CatKoishi/SAF775X-Radio/Hardware/GD32F303RC/GD32使用FPU以及DSP库的操作方法.pdf

# GD32 使用 FPU 以及 DSP 库的操作方法

在 GD32 中的 F3 系列插件有两个版本，V1.0.1 的插件是不支持 FPU 的，V2.0.0 的版本 才支持，如果安装的版本在 Target 中找不到下列的选项，请先安装新版本的插件。
在 F4 系列和 E103 系列插件都是支持 FPU 的。

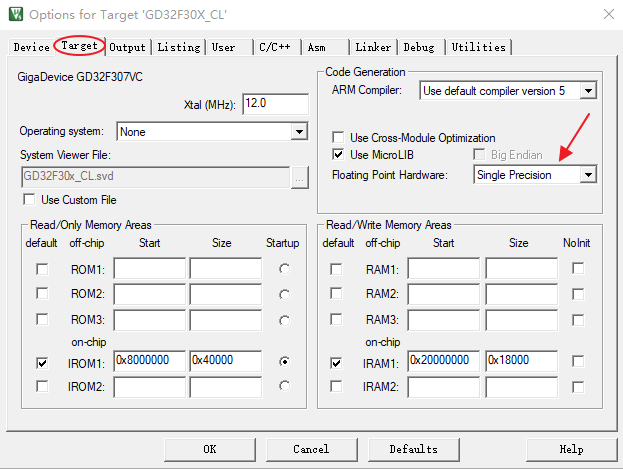
[picture p2: figure]

## 打开 FPU 的步骤

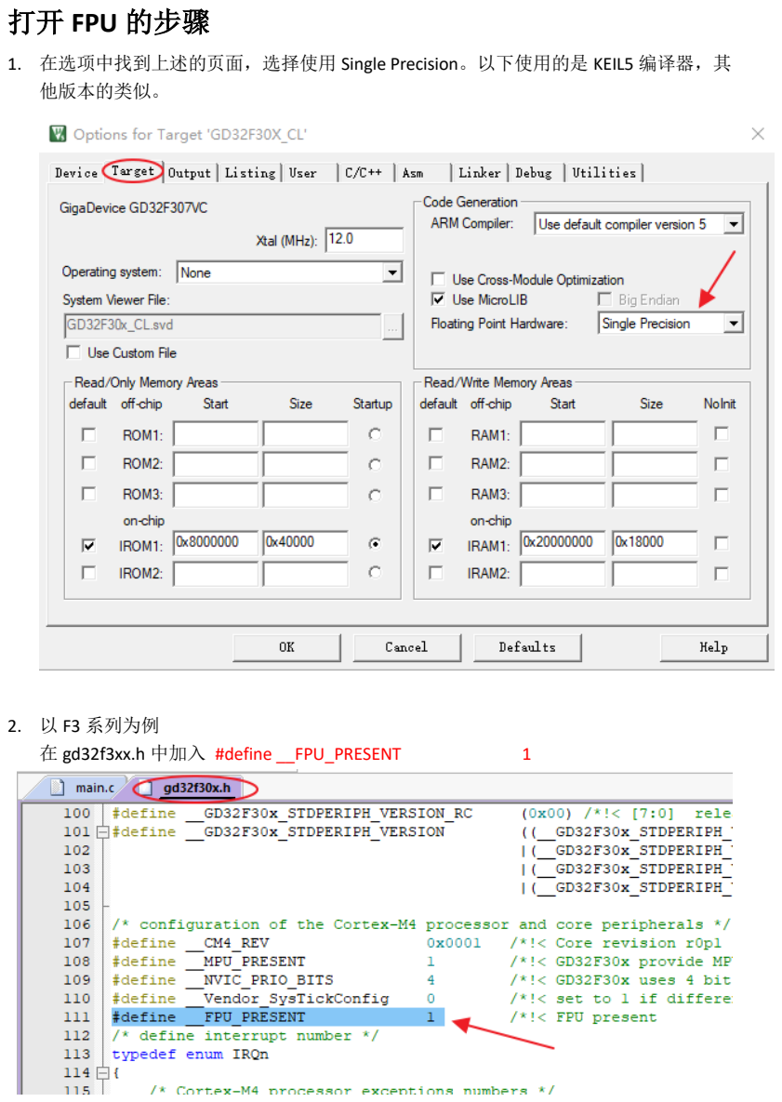
[picture p3: page 2]

1. 在选项中找到上述的页面，选择使用 Single Precision。以下使用的是 KEIL5 编译器，其 他版本的类似。
2. 以 F3 系列为例
在 gd32f3xx.h 中加入 #define __FPU_PRESENT | 1

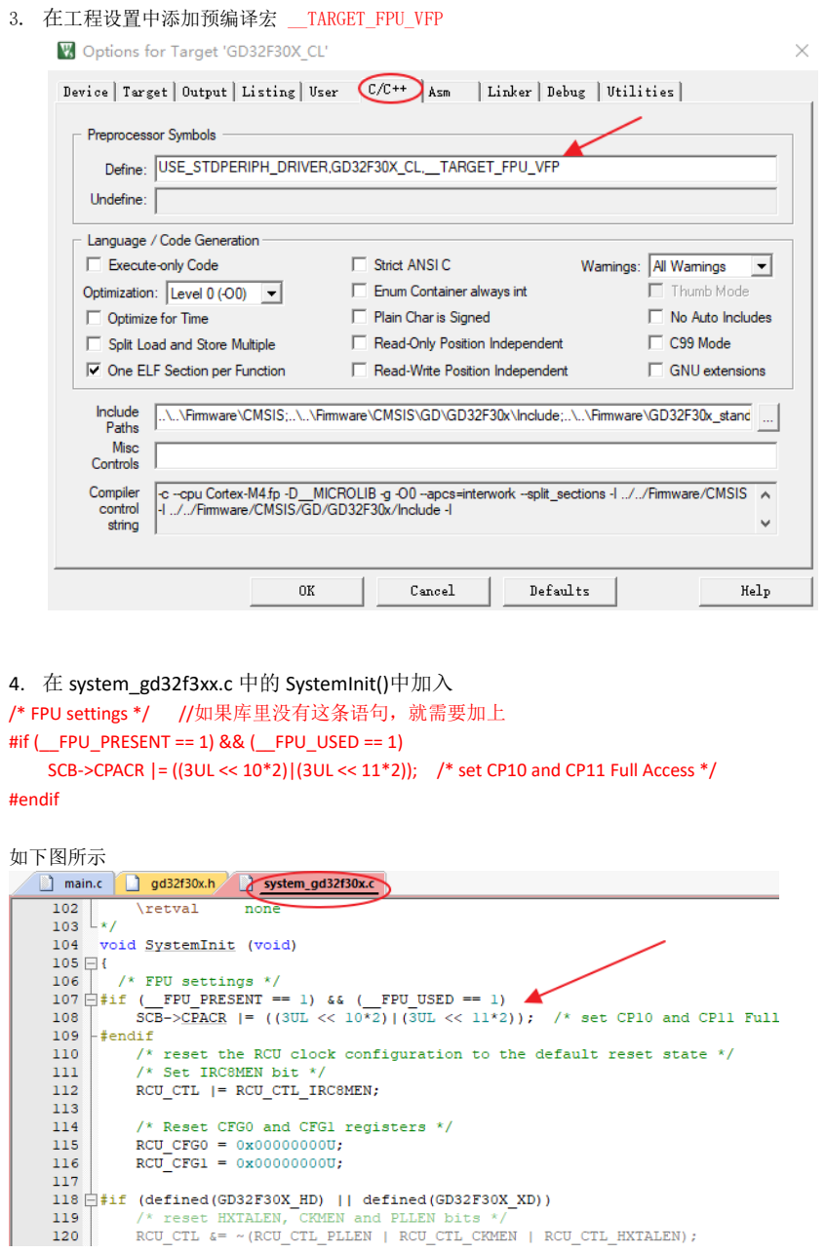
[picture p4: page 3]

3. 在工程设置中添加预编译宏 __TARGET_FPU_VFP
4. 在 system_gd32f3xx.c 中的 SystemInit()中加入
/* FPU settings */ //如果库里没有这条语句，就需要加上
#if (__FPU_PRESENT == 1) && (__FPU_USED == 1)

SCB->CPACR |= ((3UL << 10*2)|(3UL << 11*2)); /* set CP10 and CP11 Full Access */ #endif

如下图所示

使用 F4 系列和 E103 系列
1.同样在 gd32f4xx.h 中加入 #define __FPU_PRESENT | 1
2. 在工程设置中添加预编译宏 __TARGET_FPU_VFP
3.在 system_gd32f4xx.c 中的 SystemInit()中加入
/* FPU settings */ //如果库里没有这条语句，就需要加上
#if (__FPU_PRESENT == 1) && (__FPU_USED == 1)

SCB->CPACR |= ((3UL << 10*2)|(3UL << 11*2)); /* set CP10 and CP11 Full Access */ #endif
5. 重新编译下载烧录即可

## 检查 FPU 是否打开

1. 在 jlink 调试控制界面下，输入语句
mem32 0XE000ED88 1
具体看下图，得到的值为 00F0 0000，证明 FPU 已经开启

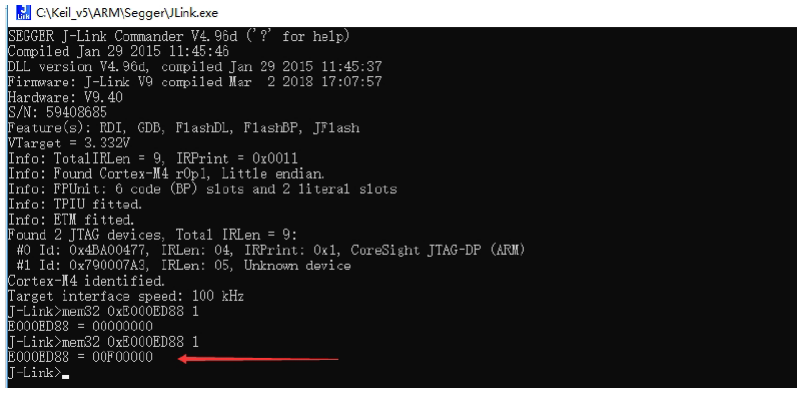
[picture p5: figure]

2. KEIL 调试浮点运算反汇编界面中会有 VLDR VADD 等浮点运算寄存器 如下图所示

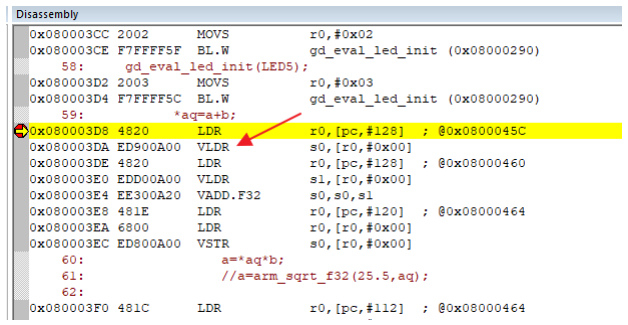
[picture p6: figure]

没开启的情况如下图

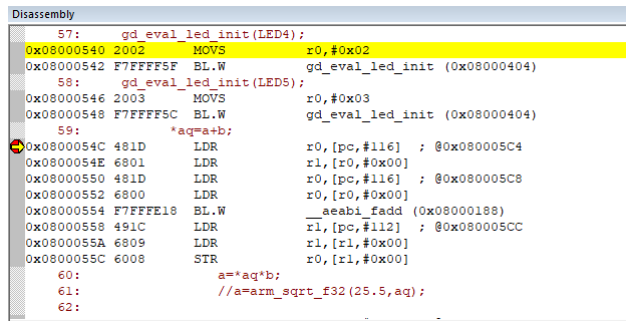
[picture p7: figure]

## 使用 DSP 的步骤

1. 打开 FPU 之后，在工程中添加 ARM 官方浮点库 ”arm_cortexM4lf_math.lib” "arm_math.h"

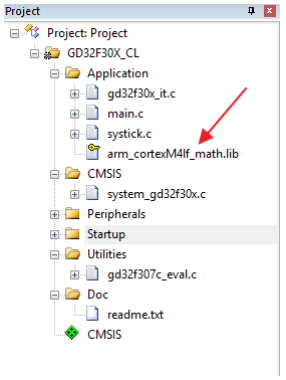
[picture p8: figure]

2. 在需要使用浮点库函数的.c 文件中添加 #include "arm_math.h" （这个头文件中包含所 有的函数接口）
3. 在工程设置中添加预编译宏 ARM_MATH_CM4

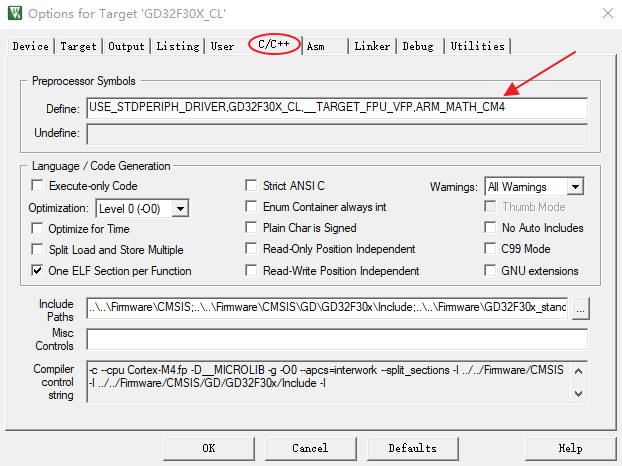
[picture p9: figure]
