CatKoishi/SAF775X-Radio/Hardware/IMG_20230905_173325.jpg

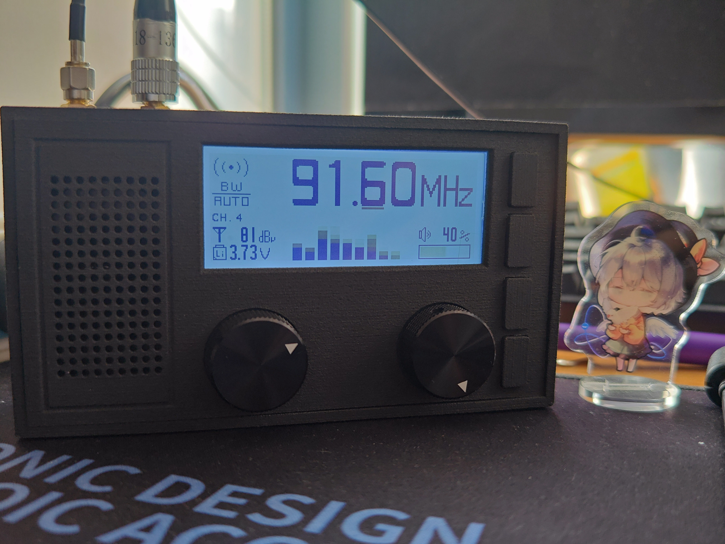
Hardware/IMG_20230905_173325.jpg
