CatKoishi/SAF775X-Radio/Hardware/GD32F303RC/MINI-GD32F303RCV4.0.pdf

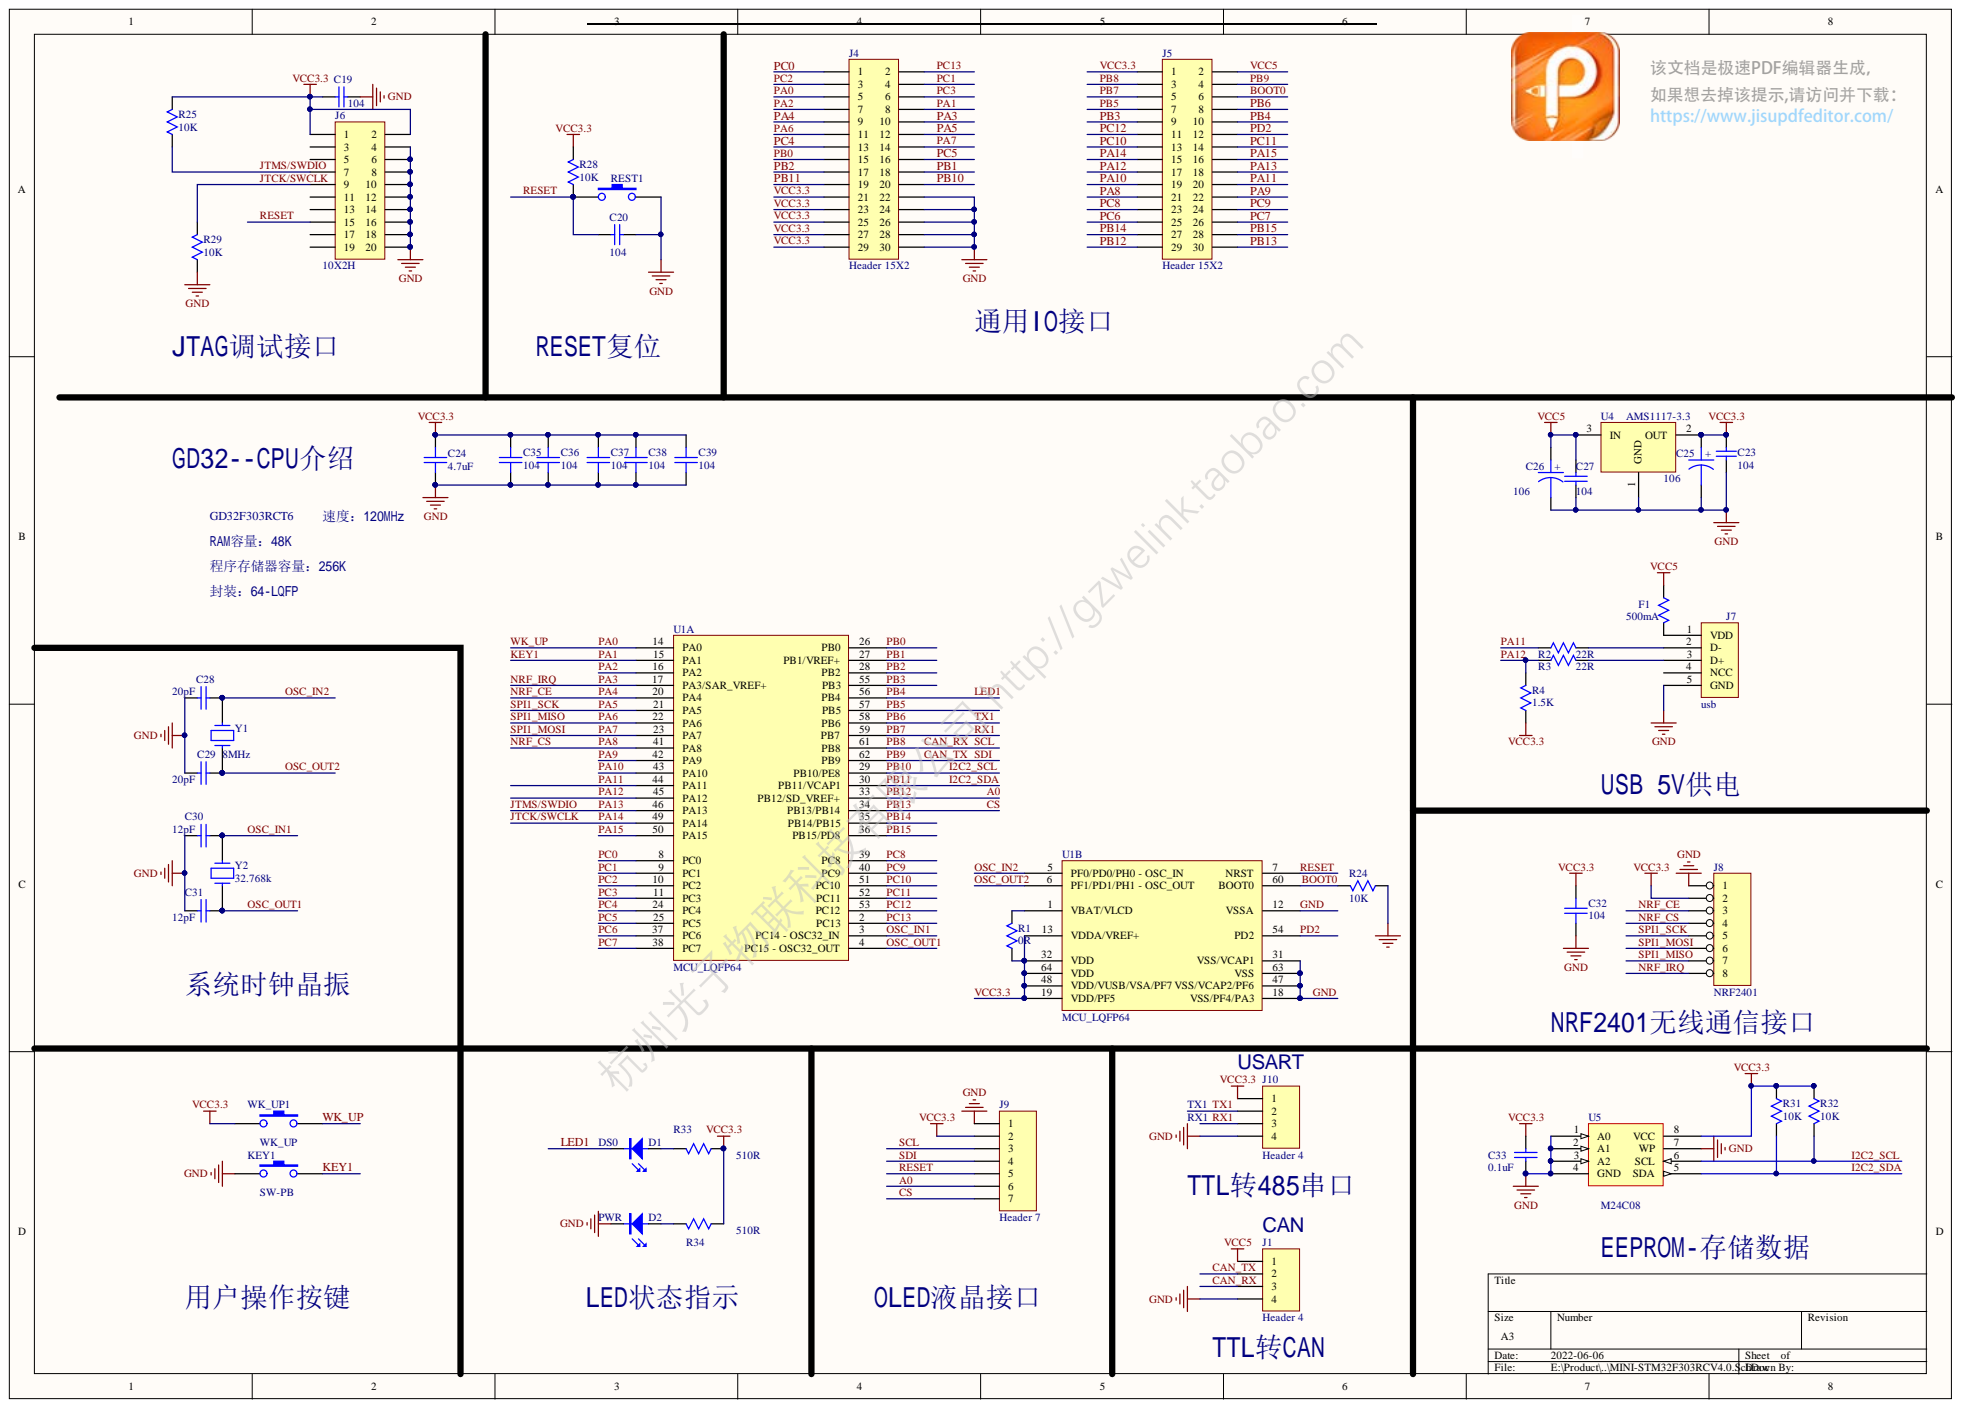
[picture p19: page 1]

该文档是极速PDF编辑器生成，
如果想去掉该提示,请访问并下载：
https://www.jisupdfeditor.com/ (https://www.jisupdfeditor.com?watermark)
