CatKoishi/SAF775X-Radio/User/hardware/SAF775X.c

#include "SAF775X.h"
#include "gd32f30x.h"
#include "stdarg.h"
#include "systick.h"
#include "iic_sw.h"
#include "Dirana3_ABB_E7A0.h"
#include "Dirana3_ABB_E7A1.h"
#include "Dirana3BasicDSP.h"

#define WORD_LOW_BYTE(a)     ((unsigned char)(a & 0x00FF))
#define WORD_HIGH_BYTE(a)    ((unsigned char)(a >> 8))
/************************************************************************************************************************************/

struct Dirana3Radio *sys;

static void SetAudioSampleRate(uint8_t sampleRate);

extern struct RDSData sRDSData;

/************************************************************************************************************************************/

const uint8_t nBandRFMode[NUM_BANDS] = 
{ RFMODE_FM, RFMODE_AM, RFMODE_AM, RFMODE_AM };

//不同波段的步进值
uint16_t nBandStep[NUM_BANDS][NUM_STEPS] = 
{
	{ 1, 10 , 0  , 0    },	//x10 KHz  FM
	{ 1,  9 , 0  , 0    },  //x1  KHz  LW
	{ 1,  9 , 100, 0    },  //x1  KHz  MW
	{ 1,  5 , 100, 1000 }   //x1  KHz  SW
};

//不同波段的步进值的数量
const uint8_t nBandStepNum[NUM_BANDS] = 
{ 2, 2, 3, 4 };

uint8_t nBandStepATS[NUM_BANDS] = 
{ 10, 1, 9, 5};

const uint16_t nFastATS[14][2] = 
{
	{2300, 2500},
	{3200, 3400},
	{3900, 4000},
	{4750, 5060},
	{5900, 6200},
	{7100, 7600},
	{9100, 10000},
	{11600, 12100},
	{13500, 13870},
	{15100, 15800},
	{17480, 17900},
	{18900, 19020},
	{21450, 21850},
	{25600, 26100}
};

const uint16_t nFMATSRegion[4][2] = {
	{8700,10800},
	{6500,7300},
	{7600,9000},
	{8750,10800},
};

const int16_t nBandFMin[NUM_BANDS] =
{ 6500, 144, 522, 2300 };

const int16_t nBandFMax[NUM_BANDS] =
{ 10800, 288, 1710, 27000 };

/************************************************************************************************************************************/

const uint8_t DSP_FIRM0_PRODUCTION[] =
{
	1,0xE8,
	0x81,0x2C,
	0
};

const uint8_t DSP_FIRM1_PRODUCTION[] =
{
	//Load Firmware Version 7.1
	25,0xE1,0x9C,0x40,0xCC,0x6B,0x8C,0x70,0xE4,0xD6,0x01,0xBB,0xDB,0x00,0x45,0x75,0x2C,0x68,0xA1,0x39,0x33,0x53,0xF5,0x4E,0x9D,0x8F,
	25,0xE1,0x2B,0xC3,0xA0,0x0D,0xC7,0x85,0xA4,0x9D,0x99,0x4D,0x5C,0x15,0x44,0x08,0x16,0x52,0x8E,0x6C,0xAA,0xF5,0xB5,0x09,0x08,0x25,
	25,0xE1,0x9A,0xBE,0xEB,0x91,0xCC,0x98,0xBC,0x4D,0x89,0x8E,0x0F,0x18,0x8C,0x3A,0xD3,0xD2,0x11,0xA7,0x49,0xE8,0x69,0x4A,0x3C,0x22,
	25,0xE1,0xA8,0x90,0xF1,0x8B,0x74,0xC3,0x97,0xA1,0xEB,0x25,0x4C,0x56,0xBC,0x29,0x46,0x85,0xA1,0x52,0x22,0x75,0x3E,0xBD,0xC6,0xFC,
	25,0xE1,0x4B,0x76,0xE7,0x85,0x74,0xBB,0x2E,0x3E,0x14,0xFE,0xAF,0xAC,0x37,0xF0,0x8A,0xA2,0x9D,0x90,0x9E,0xC3,0xC8,0xC9,0xEB,0x22,
	25,0xE1,0x6E,0x24,0x4B,0x07,0xDD,0xC5,0x43,0x36,0x0F,0x71,0x9D,0x06,0x64,0x69,0x77,0x91,0xD6,0x58,0x29,0xB4,0x41,0xFF,0xD6,0x65,
	25,0xE1,0x34,0x04,0x67,0xE1,0x77,0xC5,0x34,0xB7,0xCD,0x37,0x32,0x4E,0x56,0x9F,0x77,0xE8,0x5C,0x60,0x13,0x34,0x7E,0x44,0xD3,0xEE,
	25,0xE1,0x46,0x8F,0x9F,0x06,0xD3,0x9E,0x22,0x38,0xA0,0x62,0x28,0x45,0x26,0xC4,0x80,0x72,0xF4,0x22,0xF0,0x4B,0x45,0xD9,0xA1,0x7D,
	25,0xE1,0x54,0xD9,0x0D,0x88,0x02,0x9C,0x95,0x51,0xAE,0x97,0x91,0xA1,0xB8,0x66,0x33,0xE4,0x87,0x1D,0xC7,0xB8,0x00,0x1E,0x7B,0x30,
	25,0xE1,0x3C,0xE5,0x08,0x7F,0x39,0xC4,0x54,0x2C,0x3D,0xFF,0xAF,0xF8,0x1D,0xF5,0xDB,0x8F,0xE9,0xEE,0x9F,0x1B,0x38,0x42,0x96,0x48,
	25,0xE1,0xEB,0xFC,0x0A,0x05,0x68,0x9B,0x4E,0x9B,0xC7,0xDF,0x40,0x11,0x6E,0xFA,0x01,0x2F,0xD9,0x3E,0x60,0xEA,0xEB,0x13,0x3D,0x73,
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

void Set_REG(uint8_t addr, uint8_t* data, uint8_t size)
{
	I2C_Start(DSP_I2C_ADDR&0xFE);
	I2C_WriteByte(addr);
	
	for(uint16_t i = 0;i<size;i++)
	{
		I2C_WriteByte(data[i]);
	}
	
	I2C_Stop();
}

void Set_REGFree(int len, ...)
{
	uint8_t tmp;
	uint32_t i;
	va_list vArgs;
	va_start(vArgs, len);
	
	I2C_Start(DSP_I2C_ADDR&0xFE);
	for(i=0;i<len;i++)
	{
		tmp = va_arg(vArgs, uint32_t);
		I2C_WriteByte(tmp);
	}
	I2C_Stop();
	
	va_end(vArgs);
}


void Get_REG(uint8_t addr, uint8_t* data, uint8_t size)
{
	uint16_t i = 0;
	I2C_Start(DSP_I2C_ADDR&0xFE);
	I2C_WriteByte(addr);
	I2C_Restart(DSP_I2C_ADDR|0x01);
	
	for(i = 0;i<size-1;i++)
	{
		data[i] = I2C_ReadByte(0);
	}
	data[i] = I2C_ReadByte(1);
	
	I2C_Stop();
}

void Set_ADSP(uint32_t subaddr, uint32_t data)
{
	I2C_Start(DSP_I2C_ADDR&0xFE);
	
	I2C_WriteByte((uint8_t)(subaddr >> 16));
	I2C_WriteByte((uint8_t)(subaddr >> 8));
	I2C_WriteByte((uint8_t)subaddr);
	
	if(subaddr&0x004000)	// YMEM
	{
		I2C_WriteByte((uint8_t)(data >> 8));
		I2C_WriteByte((uint8_t)data);
	}
	else	//XMEM
	{
		I2C_WriteByte((uint8_t)(data >> 16));
		I2C_WriteByte((uint8_t)(data >> 8));
		I2C_WriteByte((uint8_t)data);
	}
	
	I2C_Stop();
}

void Set_ADSP_multi(uint32_t subaddr, uint32_t *data, uint8_t size)
{
	I2C_Start(DSP_I2C_ADDR&0xFE);
	
	I2C_WriteByte((uint8_t)(subaddr >> 16));
	I2C_WriteByte((uint8_t)(subaddr >> 8));
	I2C_WriteByte((uint8_t)subaddr);
	
	for(uint16_t i = 0;i<size;i++)
	{
		if(subaddr&0x4000)	// YMEM
		{
			I2C_WriteByte((uint8_t)(data[i] >> 8));
			I2C_WriteByte((uint8_t)data[i]);
		}
		else	//XMEM
		{
			I2C_WriteByte((uint8_t)(data[i] >> 16));
			I2C_WriteByte((uint8_t)(data[i] >> 8));
			I2C_WriteByte((uint8_t)data[i]);
		}
	}
	
	I2C_Stop();
}

uint32_t Get_ADSP(uint32_t subaddr)
{
	uint32_t data = 0;
	I2C_Start(DSP_I2C_ADDR&0xFE);
	
	I2C_WriteByte((uint8_t)(subaddr >> 16));
	I2C_WriteByte((uint8_t)(subaddr >> 8));
	I2C_WriteByte((uint8_t)subaddr);
	
	I2C_Restart(DSP_I2C_ADDR|0x01);
	
	if(subaddr&0x4000)	// YMEM
	{
		data  = (uint32_t)I2C_ReadByte(0) << 8;
		data |= (uint32_t)I2C_ReadByte(1);
	}
	else	//XMEM
	{
		data  = (uint32_t)I2C_ReadByte(0) << 16;
		data |= (uint32_t)I2C_ReadByte(0) << 8;
		data |= (uint32_t)I2C_ReadByte(1);
	}
	
	I2C_Stop();
	
	return data;
}

void WaitBusy(void)
{
	delay_ms(1);
	while(1)
	{
		if(gpio_input_bit_get(GPIOA,GPIO_PIN_15) == SET)
			break;
	}
}

/**
 * @brief  发送DSP软件数据
 * @param  data 软件数据指针
 */
void DSP_WRITE_DATA(const uint8_t* data)
{
	uint8_t len;
	uint8_t *pa = (uint8_t *)data;	//指针复制
	for (;;)
	{
		len = *pa;
		pa++;
		if (!len)  // len = 0, transmit complete
			break;
		if(len == 0xFF)  // len = 0xFF, Wait SAF775X Ready
		{
			WaitBusy();
			continue;
		}
		if (len & 0x80)  // len = 0x80, delay
		{
			delay_ms(((uint16_t)(len & 0x7f) << 8) | *(pa++));
		}
		else
		{
			I2C_Transmit(DSP_I2C_ADDR, pa, len);
			pa = pa + len;
		}
	}
}


void BootDirana3(void)
{
	gpio_bit_reset(GPIOC, GPIO_PIN_10);
	delay_ms(5);
	gpio_bit_set(GPIOC, GPIO_PIN_10);
	delay_ms(20);
	
	if(sys->Config.bDemoMode == true)
		DSP_WRITE_DATA(DSP_KEYCODE_PRODUCTION);
	
	DSP_WRITE_DATA(DSP_FIRM0_PRODUCTION);
	
	DSP_WRITE_DATA(DSP_INIT);
}

/****************************************************************/

void GetStatus(void)
{
	uint8_t rxSeq[5];
	
	Get_REG(0x00, rxSeq, 5);
	sys->Status.nQRS = (rxSeq[0]>>5)&0x07;
	sys->Status.bSTIN = (rxSeq[0]>>3)&0x01;
	sys->Status.nRSSI = ((rxSeq[1]>>1)&0x7F)-8;
	
	if(sys->Radio.nBandMode == BAND_FM)
	{
		sys->Status.nUSN = rxSeq[2];
		sys->Status.nWAM = rxSeq[3];
	}
	else
	{
		sys->Status.nACD = rxSeq[2];
	}
	sys->Status.nOffset = rxSeq[4]&0x7F;
	if(rxSeq[4]&0x80)
		sys->Status.nOffset = -sys->Status.nOffset;
	
}

void GetQRS(void)
{
	uint8_t rxSeq;
	Get_REG(0x00, &rxSeq, 1);
	sys->Status.nQRS = (rxSeq>>5)&0x07;
	sys->Status.bSTIN = (rxSeq>>3)&0x01;
}

void GetRDS(struct RDSBuffer* rds)
{
	uint8_t sts[12];
	
	if(sys->Status.nRSSI < 20 || sys->Radio.nBandMode != BAND_FM)
		return;
	
	Get_REG(0x07, sts, 1);
	
	rds->status  = sts[0];
	//BIT  |  7   |  6   |   5   |   4   | 3 | 2 |  1   | 0 |
	//FUNC | RDAV | DOFL | SDATA | TBGRP | / | / | SYNC | / |
	if( ((rds->status & 0x80) != 0) && ((rds->status & 0x20) == 0) )
	{
		Get_REG(0x07, sts, 10);
		rds->status  = sts[0];
		rds->block_A = (((uint16_t)sts[1]) << 8) + sts[2];
		rds->block_B = (((uint16_t)sts[3]) << 8) + sts[4];
		rds->block_C = (((uint16_t)sts[5]) << 8) + sts[6];
		rds->block_D = (((uint16_t)sts[7]) << 8) + sts[8];
		rds->error   = sts[9];
		DecodeRDS(rds);
	}
	
}


/**
 * @brief  设置音量
 * @param  percent 音量大小 0~100
 */
void SetVolume(uint8_t percent)
{
	float VoldB;
	if(percent > MAX_VOL)
		return;
	sys->Audio.nVolume[sys->Audio.index] = percent;
	if(percent < 4)
		VoldB = -67 + 4*percent;
	else
		VoldB = (-0.53125)*(100-percent);
	if(sys->Audio.index == 0)  // headphone
	{
		setFader('F', VoldB);
	}
	else  // speaker
	{
		setFader('R', VoldB);
	}
}

void SetMute(bool mute)
{
	sys->Audio.bMuted = mute;
	
	if(sys->Audio.bMuted == true)
	{
		setMute(ADSP_MUTE_MAIN, 1);
	}
	else if(sys->Audio.bMuted == false)
	{
		setMute(ADSP_MUTE_MAIN, 0);
	}
}

void TuneFreq(uint16_t freq, uint8_t mode)
{
	uint8_t str[3] = {0,0,0};
	sys->Radio.nBandFreq[sys->Radio.nBandMode] = freq;
	
	str[0] = (mode<<4) + sys->Radio.nBandMode;
	str[1] = WORD_HIGH_BYTE(freq);
	str[2] = WORD_LOW_BYTE(freq);
	Set_REG(0x00, str, 3);
}

/**************/

void SetTuner(void)
{
	uint8_t data = 0;;
	data = (sys->Config.nBandAGC[sys->Radio.nRFMode]<<6) + sys->Config.nBandFilter[sys->Radio.nRFMode];
	Set_REG(0x03, &data, 1);
}

/**
 * @brief  设置收音FIR滤波器带宽 
 * @param  f 带宽		[0-15] -> [自动,72,89,107,124,141,159,176,193,211,228,245,262,280,297,314]
 *					        [0-15] -> [自动,2,2.2,2.4,2.7,3.0,3.3,3.6,4.0,4.4,4.9,5.4,5.9,6.6,7.2,8.0]
 */
void SetFilter(uint8_t index)
{
	if(index >= 16)
		return;
	sys->Config.nBandFilter[sys->Radio.nRFMode] = index;
	SetTuner();
}

void SetAGC(uint8_t index)
{
	if(index >= 4)
		return;
	sys->Config.nBandAGC[sys->Radio.nRFMode] = index;
	SetTuner();
}

/**************/

void SetTunerOPT(void)
{
	uint8_t data = 0;
	uint8_t data2 = 0;
	if(sys->Radio.nRFMode == RFMODE_FM)
	{
		sys->Config.bFMAGCext ? (data |= 0x80):(data &= 0x7F);
		data2 = data;
		data |= (sys->Config.nFMANTsel << 2)&0x04;
		if(data & 0x04)
			data2 &= 0xFB;
		else
			data2 |= 0x04;
		sys->Config.bFMiPD ? (data |= 0x01):(data &= 0xFE);
	}
	else
	{
		sys->Config.bAMANTtyp ? (data |= 0x80):(data &= 0x7F);
	}
	
	Set_REG(0x04, &data, 1);
	Set_REG(0x64, &data2, 1);
}

void SetExtAGC(bool on)
{
	sys->Config.bFMAGCext = on;
	//set gpio
	SetTunerOPT();
}

void SetFMAntenna(uint8_t ant)
{
	if(ant > 1)
		return;
	sys->Config.nFMANTsel = ant;
	SetTunerOPT();
}

void SetFMiPhaseDiversity(bool on)
{
	if(sys->Config.bDemoMode == false)
		return;
	sys->Config.bFMiPD = on;
	SetTunerOPT();
}

void SetAMAntenna(uint8_t ant_type)
{
	if(ant_type > 1)
		return;
	sys->Config.bAMANTtyp = ant_type;
	// go to idle/standby
	SetTunerOPT();
	// return normal state
}

/**************/

void SetRadioDSP(void)
{
	uint8_t data = 0;
	
	if(sys->Radio.nRFMode == RFMODE_FM)
	{
		sys->Config.bFMiMS ? (data |= 0x80):(data &= 0x7F);
		sys->Config.bFMCNS ? (data |= 0x40):(data &= 0xBF);
		sys->Config.bFMCEQ ? (data |= 0x20):(data &= 0xDF);
		data |= (sys->Config.nNBSA[sys->Radio.nRFMode]<<2)&0x0C;
		data |= 0x02;
	}
	else
	{
		data |= 0x40;
		data |= (sys->Config.nNBSA[sys->Radio.nRFMode]<<2)&0x0C;
		data |= (sys->Config.nNBSB)&0x03;
	}
	
	Set_REG(0x05, &data, 1);
}

void SetFMiMultipathSuppression(bool on)
{
	sys->Config.bFMiMS = on;
	SetRadioDSP();
}

void SetFMClickNoiseSuppression(bool on)
{
	sys->Config.bFMCNS = on;
	SetRadioDSP();
}

void SetFMChannelEqualizer(bool on)
{
	if(sys->Config.bDemoMode == false)
		return;
	sys->Config.bFMCEQ = on;
	SetRadioDSP();
}

void SetNoiseBlanker(uint8_t rfmode, uint8_t sensIF, uint8_t sensAu)
{
	if(sensIF >= 4 || sensAu >= 4)
		return;
	sys->Config.nNBSA[rfmode] = sensIF;
	sys->Config.nNBSB = sensAu;
	SetRadioDSP();
}

/**************/

void SetRadioSignal(void)
{
	uint8_t data = 0;
	if(sys->Radio.nRFMode == RFMODE_FM)
	{
		if(sys->Config.bForceMono == true || sys->Config.nFMST == 0)
			data |= 1<<7;
		if(sys->Config.bFMSI == true)
			data |= 1<<5;
		
		data |= sys->Config.nDeemphasis;
	}
	else
	{
		data |= (sys->Config.nAMFixedHP<<2) + sys->Config.nAMFixedLP;
	}
	Set_REG(0x06, &data, 1);
  Set_REG(0x66, &data, 1);
}

// Attack --> Mono
// Decay  --> Stereo

// Mono Low Default High Full
const uint8_t stereoLevel[5][7] = {
  { 0x72, 0x3F, 0x4A, 0x33, 0x00, 0x3F, 0x13 },  // 
  { 0x72, 0x3F, 0x4A, 0x33, 0x00, 0x3F, 0x13 },  // 
  { 0x72, 0x3F, 0x4A, 0x33, 0x00, 0x3F, 0x13 },  // Default
  { 0x72, 0x3F, 0x4A, 0x33, 0x00, 0x3F, 0x13 },  // 
  { 0x72, 0x3F, 0x4A, 0x33, 0x00, 0x3F, 0x13 }   // 
};

// Mono Low Default High Full
const int8_t fmsiLevel[5][9] = {
  { 0x00, 0x32, 0x00, 0x32, 28, 36, 52, 84, 32 },  // 
  { 0x00, 0x64, 0x00, 0x64, 36, 40, 63, 90, 0  },  // 
  { 0x00, 0x32, 0x00, 0x32, 28, 36, 52, 84, 32 },  // Default
  { 0x00, 0x14, 0x00, 0x14, 28, 20, 32, 54, 48 },  // 
  { 0x00, 0x01, 0x00, 0x01, 24, 14, 24, 40, 64 },  // 
};


void SetFMStereo(uint8_t level)
{
  if(level > 4)
    return;
  
  uint8_t txd[5] = { 0 };
  sys->Config.nFMST = level;
  SetRadioSignal(); // Set ForceMono & FMSI
  
  if(sys->Radio.nRFMode != RFMODE_FM)
    return;
  
  if(sys->Config.bFMSI == true) {
    Set_REGFree(2,0x19,0);
    Set_REGFree(2,0x79,0);
    Set_REGFree(2,0x1D,0);
    Set_REGFree(2,0x7D,0);
    
    for(int i = 0; i < 2; i++) {
      txd[0] = 0x01+i*16;
      txd[1] = fmsiLevel[level][0], txd[2] = fmsiLevel[level][1];
      txd[3] = fmsiLevel[level][2], txd[4] = fmsiLevel[level][3];
      Set_REG(0xC7, txd, 5);
      
      txd[0] = 0x02+i*16;
      txd[1] = fmsiLevel[level][4], txd[2] = fmsiLevel[level][5];
      txd[3] = fmsiLevel[level][6], txd[4] = fmsiLevel[level][7];
      Set_REG(0xC7, txd, 5);
      
      txd[0] = 0x03+i*16;
      txd[1] = fmsiLevel[level][8];
      Set_REG(0xC7, txd, 2);
    }
    
  } else {
    Set_REG(0x18, (uint8_t*)stereoLevel[level], 7);
    Set_REG(0x78, (uint8_t*)stereoLevel[level], 7);
  }
  
}

void SetFMStereoImprovement(bool on)
{
	if(sys->Config.bDemoMode == false)
		return;
	sys->Config.bFMSI = on;
	SetFMStereo(sys->Config.nFMST);
}

void SetFMDeemphasis(uint8_t tao)
{
	sys->Config.nDeemphasis = tao;
	SetRadioSignal();
}

void SetAMFixedHP(uint8_t hp)
{
	sys->Config.nAMFixedHP = hp;
	SetRadioSignal();
}

void SetAMFixedLP(uint8_t lp)
{
	sys->Config.nAMFixedLP = lp;
	SetRadioSignal();
}

/**************/

void SetRadioAutoBW(uint8_t sens, uint8_t lev)
{
	uint8_t data = 0;
	if(sys->Radio.nRFMode != RFMODE_FM)
		return;
	
	data |= (sens<<2)+lev;
	Set_REG(0x07, &data, 1);
}

/**************/

void SetSoftMute(uint8_t level)
{
	// addr time func rssi usn/mph attenuation
	// 0x0D,0x65,0x10,0x3A,0x33,0x0C | default value
	if(sys->Radio.nRFMode == RFMODE_FM)
	{
		switch(level)
		{
			case 0:Set_REGFree(6,0x0D,0x65,0x00,0x3A,0x33,0x0C);break;  // off
			case 1:Set_REGFree(6,0x0D,0x65,0x10,0x15,0x33,0x0C);break;  // 
			case 2:Set_REGFree(6,0x0D,0x65,0x10,0x3A,0x33,0x0C);break;  // default value
			case 3:Set_REGFree(6,0x0D,0x65,0x1E,0x3A,0x33,0x08);break;  // 
			case 4:Set_REGFree(6,0x0D,0x65,0x2A,0x3A,0x55,0x05);break;  // full control
		}
	}
	else
	{
		switch(level)
		{
			case 0:Set_REGFree(6,0x0D,0x60,0x00,0x3A,0x33,0x0C);break;  // off
			case 1:Set_REGFree(6,0x0D,0x60,0x10,0x3A,0x33,0x0C);break;  // 
			case 2:Set_REGFree(6,0x0D,0x60,0x90,0x3A,0x33,0x0C);break;  // default value
			case 3:Set_REGFree(6,0x0D,0x60,0xD0,0x49,0x33,0x05);break;  // 
			case 4:Set_REGFree(6,0x0D,0x60,0xD0,0x4D,0x33,0x04);break;  // full control
		}
	}
}

/**************/



/**************/

void SwitchBand(uint8_t band)
{
	if(band >= NUM_BANDS)
		return;
	sys->Radio.nBandMode = band;
	sys->Radio.nRFMode = nBandRFMode[band];
	
	setMute(ADSP_MUTE_MAIN, 1);
	TuneFreq(sys->Radio.nBandFreq[sys->Radio.nBandMode], Preset);
	SetTuner();
	SetTunerOPT();
	SetRadioDSP();
  SetFMStereo(sys->Config.nFMST);
	SetRadioAutoBW(1,2);
	SetSoftMute(sys->Config.nSoftMute[sys->Radio.nRFMode]);
	
	SetMute(sys->Audio.bMuted);
}


void TunerStructInit(struct Dirana3Radio* init, bool initPara)
{
	sys = init;
	if(initPara)
	{
		sys->Config.bDemoMode = true;
		
		sys->Config.nBandAGC[0] = 0;
		sys->Config.nBandAGC[1] = 0;
		sys->Config.nBandFilter[0] = 0;
		sys->Config.nBandFilter[1] = 0;
		sys->Config.bFMAGCext = 1;
		sys->Config.nFMANTsel = 0;
		sys->Config.bFMiPD = 0;
		sys->Config.bFMiMS = 1;
		sys->Config.bFMCNS = 1;
		sys->Config.bFMCEQ = 1;
		sys->Config.bFMSI = 1;
		sys->Config.nNBSA[RFMODE_FM] = 1;
		sys->Config.nNBSA[RFMODE_AM] = 3;
		 
		sys->Config.nFMST = 1;
    sys->Config.bForceMono = false;
		sys->Config.nDeemphasis = 1;
		
		sys->Config.bAMANTtyp = 0;
		sys->Config.nAMFixedHP = 1;
		sys->Config.nAMFixedLP = 1;
		
		sys->Radio.nBandMode = BAND_FM;
		sys->Radio.nRFMode = RFMODE_FM;
		sys->Radio.nBandFreq[0] = 9160;
		sys->Radio.nBandFreq[1] = 210;
		sys->Radio.nBandFreq[2] = 639;
		sys->Radio.nBandFreq[3] = 9400;
		sys->Radio.nFreqStep[0] = 1;
		sys->Radio.nFreqStep[1] = 1;
		sys->Radio.nFreqStep[2] = 1;
		sys->Radio.nFreqStep[3] = 1;
		
		sys->Audio.bMuted = false;
		sys->Audio.nVolume[0] = 40;
		sys->Audio.nVolume[1] = 50;
		sys->Audio.index = 0;
		
		sys->ATS.nATSMode = 1;
		sys->ATS.nFMRegion = 0;
		sys->ATS.nSigThreshold = 23;
		sys->ATS.nMWStep = 9;
	}
}

/**
 * @brief SAF7751初始化
 * @param audioSampleRate 全局音频采样率，仅允许 44.1 kHz 或 48 kHz
 */
void TunerInit(uint8_t audioSampleRate)
{
	BootDirana3();
	SetAudioSampleRate(audioSampleRate);

	SetTuner();
	SetTunerOPT();
	SetRadioDSP();
  SetFMStereo(sys->Config.nFMST);
	SetRadioSignal();
	SetRadioAutoBW(1,2);
	SetSoftMute(sys->Config.nSoftMute[sys->Radio.nRFMode]);
  
	TuneFreq(sys->Radio.nBandFreq[sys->Radio.nBandMode], Preset);
}

/**
 * @brief 设置 SAF775x 全局音频采样率
 * @param sampleRate 采样率寄存器值，0 为 44.1 kHz，1 为 48 kHz
 */
static void SetAudioSampleRate(uint8_t sampleRate)
{
	// 调用方传入非法值时保持原有 44.1 kHz 行为。
	if(sampleRate > AUDIO_SAMPLE_RATE_48K)
		sampleRate = AUDIO_SAMPLE_RATE_44K1;

	setADSPSampleRate(sampleRate == AUDIO_SAMPLE_RATE_48K ? 48000.0f : 44100.0f);
	Set_REGFree(2, 0x3F, sampleRate);
}

void SetCoaxOutput(bool on)
{
	if(on)
	{
		// Route the currently active analog output path to SPDIF output so coax
		// follows the user's active volume path while analog behavior stays unchanged.
		// SPDIFxOutpntr is a stereo pointer.
		// UM SAF775x 2.3.3, Table 28:
		// SPDIF output mode 0 -> Transmit enable, Bypass off.
		if(sys->Audio.index == 0)
		{
			Set_ADSP(ADSP_X_SPDIF0Outpntr, ADSP_X_FrontOutL_REL);
			Set_ADSP(ADSP_X_SPDIF1Outpntr, ADSP_X_FrontOutL_REL);
		}
		else
		{
			Set_ADSP(ADSP_X_SPDIF0Outpntr, ADSP_X_RearOutL_REL);
			Set_ADSP(ADSP_X_SPDIF1Outpntr, ADSP_X_RearOutL_REL);
		}
		Set_REGFree(3, 0xA9, 0x22, 0x00);
		Set_REGFree(3, 0xA9, 0x23, 0x00);
	}
	else
	{
		Set_REGFree(3, 0xA9, 0x22, 0x02);
		Set_REGFree(3, 0xA9, 0x23, 0x02);
	}
}

void SetHostI2S0Output(bool on)
{
	if(on)
	{
		// Route local processed audio to Host I2S output 0.
		// HIIS0Outpntr is a stereo pointer, so FrontOutL routes FrontOutL/FrontOutR.
		// UM SAF775x 2.3.2:
		//   0x1A = 0 -> Philips format for Host I2S outputs
		//   0x16 = 0 -> Host I2S output 0 enabled
		Set_REGFree(3, 0xA9, 0x1A, 0x00);
		Set_REGFree(3, 0xA9, 0x16, 0x00);
		Set_ADSP(ADSP_X_HIIS0Outpntr, ADSP_X_FrontOutL_REL);
	}
	else
	{
		Set_REGFree(3, 0xA9, 0x16, 0x01);
	}
}
