CatKoishi/SAF775X-Radio/User/main.h

/*!
    \file    main.h
    \brief   the header file of main 

    \version 2017-02-10, V1.0.0, firmware for GD32F30x
    \version 2018-10-10, V1.1.0, firmware for GD32F30x
    \version 2018-12-25, V2.0.0, firmware for GD32F30x
    \version 2020-09-30, V2.1.0, firmware for GD32F30x 
*/

/*
    Copyright (c) 2020, GigaDevice Semiconductor Inc.

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
    1. Redistributions of source code must retain the above copyright notice, this 
       list of conditions and the following disclaimer.
    2. Redistributions in binary form must reproduce the above copyright notice, 
       this list of conditions and the following disclaimer in the documentation 
       and/or other materials provided with the distribution.
    3. Neither the name of the copyright holder nor the names of its contributors 
       may be used to endorse or promote products derived from this software without 
       specific prior written permission.

    THIS SOFTWARE IS PROVIDED BY THE COPYRIGHT HOLDERS AND CONTRIBUTORS "AS IS" 
AND ANY EXPRESS OR IMPLIED WARRANTIES, INCLUDING, BUT NOT LIMITED TO, THE IMPLIED 
WARRANTIES OF MERCHANTABILITY AND FITNESS FOR A PARTICULAR PURPOSE ARE DISCLAIMED. 
IN NO EVENT SHALL THE COPYRIGHT HOLDER OR CONTRIBUTORS BE LIABLE FOR ANY DIRECT, 
INDIRECT, INCIDENTAL, SPECIAL, EXEMPLARY, OR CONSEQUENTIAL DAMAGES (INCLUDING, BUT 
NOT LIMITED TO, PROCUREMENT OF SUBSTITUTE GOODS OR SERVICES; LOSS OF USE, DATA, OR 
PROFITS; OR BUSINESS INTERRUPTION) HOWEVER CAUSED AND ON ANY THEORY OF LIABILITY, 
WHETHER IN CONTRACT, STRICT LIABILITY, OR TORT (INCLUDING NEGLIGENCE OR OTHERWISE) 
ARISING IN ANY WAY OUT OF THE USE OF THIS SOFTWARE, EVEN IF ADVISED OF THE POSSIBILITY 
OF SUCH DAMAGE.
*/

#ifndef MAIN_H
#define MAIN_H

#include "stdbool.h"
#include "gd32f30x.h"
#include "SAF775X.h"

#define MENU_MAIN_INDEX    6
#define MENU_DISP_INDEX    7
#define MENU_AUDIO_INDEX    9
#define MENU_RADIO_INDEX    12
#define MENU_ATS_INDEX    6
#define MENU_DEVICE_INDEX    9

#define CFG_ALL    15
#define CFG_DEVICE  0
#define CFG_RADIO   1
#define CFG_DISP    2
#define CFG_AUDIO   3

#define FLASH_FM      16
#define FLASH_LW      17
#define FLASH_MW      18
#define FLASH_SW      19

typedef struct _TIME
{
	uint8_t second;
	uint8_t minute;
	uint8_t hour;
	uint8_t day;
	uint8_t month;
	uint16_t year;
	uint32_t timestamp;
}TIME;

struct info
{
	uint32_t pid[4]; // flashID | master | subversion | date
	uint32_t uid[3]; // 96bit
	uint32_t tid;
};

struct device
{
	struct info sInfo;
	TIME sTime;
	uint16_t nBatVolt;
  int8_t nIntTemp;
	uint8_t bAutoMono;
	uint8_t bCoaxEnable;
	uint8_t bI2SOutEnable;
  uint8_t nAudioSampleRate;
  uint8_t bEncoderSwap;
	uint8_t bSoftReboot;
};

typedef struct {
  uint8_t chanMax;
  uint8_t chanNum;
  uint8_t nowIndex;
  uint16_t chanFreq[CHS_MAX];
}CHANNEL;

extern struct device sDevice;
extern struct RDSData sRDSData;

void EXTI_Callback(uint8_t exti_line);
void TIM_Callback(uint8_t tim);
void ADC_Callback(uint8_t adc, char group);
void RTC_Callback(uint8_t line);

#endif /* MAIN_H */
