CatKoishi/SAF775X-Radio/User/hardware/pic.c

#include "pic.h"

/**************************16x16 icon*****************************************/

const unsigned char img_antenna[64] = { /* 0X02,0X02,0X10,0X00,0X10,0X00, */
0X00,0X00,0X3C,0X3F,0X3C,0X3C,0X3C,0X3F,0X3F,0X3C,0X3C,0X3C,0X3F,0X3C,0X00,0X00,
0X00,0X00,0X00,0X00,0XC0,0X30,0X0C,0XFF,0XFF,0X0C,0X30,0XC0,0X00,0X00,0X00,0X00,
0X00,0X00,0X00,0X00,0X00,0X00,0X00,0XFF,0XFF,0X00,0X00,0X00,0X00,0X00,0X00,0X00,
0X00,0X00,0X00,0X00,0X00,0X00,0X00,0XFC,0XFC,0X00,0X00,0X00,0X00,0X00,0X00,0X00,
};


const unsigned char img_bat[64] = { /* 0X02,0X02,0X10,0X00,0X10,0X00, */
0X00,0X00,0X03,0X03,0X3F,0X33,0X33,0X33,0X33,0X33,0X33,0X3F,0X03,0X03,0X00,0X00,
0X00,0X00,0XFF,0X00,0X00,0X0F,0X00,0X00,0X00,0X00,0X03,0X00,0X00,0XFF,0X00,0X00,
0X00,0X00,0XFF,0X00,0X00,0XFF,0X03,0X03,0X00,0X00,0X3F,0X00,0X00,0XFF,0X00,0X00,
0X00,0X00,0XFC,0XCC,0X3C,0X0C,0X0C,0X0C,0X0C,0X0C,0X0C,0X0C,0X0C,0XFC,0X00,0X00,
};


const unsigned char img_batLow[64] = { /* 0X02,0X02,0X10,0X00,0X10,0X00, */
0X00,0X00,0X03,0X03,0X3F,0X33,0X33,0X33,0X33,0X33,0X33,0X3F,0X03,0X03,0X00,0X00,
0X00,0X00,0XFF,0X00,0X00,0X00,0X00,0X3F,0X3F,0X00,0X00,0X00,0X00,0XFF,0X00,0X00,
0X00,0X00,0XFF,0X00,0X00,0X00,0X00,0XF3,0XF3,0X00,0X00,0X00,0X00,0XFF,0X00,0X00,
0X00,0X00,0XFC,0XCC,0X3C,0X0C,0X0C,0XCC,0XCC,0X0C,0X0C,0X0C,0X0C,0XFC,0X00,0X00,
};


const unsigned char img_channel[64] = { /* 0X02,0X02,0X10,0X00,0X10,0X00, */
0X00,0X3F,0X3F,0X3C,0X3C,0X00,0X3F,0X3F,0X00,0X00,0X3F,0X3F,0X00,0X00,0X00,0X00,
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
0X30,0XC3,0XC0,0XC3,0XCC,0XF3,0XC0,0XF0,0XC3,0XFC,0XC3,0XFF,0XCC,0XF3,0XCF,0XC0,
0XCC,0X00,0X0F,0XCC,0X3C,0X30,0XFF,0X00,0XFC,0XFC,0XC3,0XC0,0XC0,0XC0,0XCC,0X3F,
0XF3,0X00,0XFC,0XC3,0XCC,0X0C,0X03,0X00,0XFF,0X3C,0XF0,0XCF,0X3F,0X0C,0X3C,0XCC,
0XF0,0XFF,0X00,};
