CatKoishi/SAF775X-Radio/User/hardware/Dirana3_ABB_E7A1.h

/******************************************************************************/
/*                                                                            */
/*  (c) 2015 NXP B.V., All rights reserved                                    */
/*                                                                            */
/*  This source code and any compilation or derivative thereof is the         */
/*  proprietary information of NXP B.V. and is confidential in nature.        */
/*  Under no circumstances is this software to be exposed to or placed        */
/*  under an Open Source License of any type without the expressed            */
/*  written permission of NXP B.V..                                           */
/*                                                                            */
/******************************************************************************/

/****************************************************************************** 
 *  C-Header file for Dirana3 Audio Software 8.0                              * 
 ****************************************************************************** 
 *                                                                            
 *  $Revision: 4723 $                                                         
 *                                                                            
 *  $Date: 2015-04-13 14:51:45 +0530 (Mon, 13 Apr 2015) $                     
 *                                                                            
 *                                                                            
 *  File name:     Dirana3_ABB_E7A1.h                                         
 *                                                                            
 *  Purpose:       This file contains defines for all handles that are        
 *                 mentioned in the audio user manual version TBD             
 *                 The addresses are only valid for Dirana3 Audio Software    
 *                 version 7.2                                                
 *                                                                            
 ******************************************************************************/

#ifndef DIRANA3_ABB_E7A1_H


/* Memory offsets of ADSP */
#define ADSP_X_OFFSET                                            0xF40000UL
#define ADSP_Y_OFFSET                                            0xF44000UL


/* ADSP X memory */
#define ADSP_X_AIN01InL                                          0xF400AEUL
#define ADSP_X_AIN01InR                                          0xF400AFUL
#define ADSP_X_AIN23InL                                          0xF400B0UL
#define ADSP_X_AIN23InR                                          0xF400B1UL
#define ADSP_X_AIN45InL                                          0xF400B2UL
#define ADSP_X_AIN45InR                                          0xF400B3UL
#define ADSP_X_ALE_InPntr                                        0xF405C8UL
#define ADSP_X_ALE_OutL                                          0xF401CBUL
#define ADSP_X_ALE_OutR                                          0xF401CCUL
#define ADSP_X_ALE_PAR_EQU_LinRefSpecSq1                         0xF40EB2UL
#define ADSP_X_ALE_PAR_EQU_LinRefSpecSq2                         0xF40EB3UL
#define ADSP_X_ALE_PAR_EQU_LinRefSpecSq3                         0xF40EB4UL
#define ADSP_X_ALE_PAR_EQU_OnOff                                 0xF40EAEUL
#define ADSP_X_ALE_PAR_Gain1                                     0xF40EBEUL
#define ADSP_X_ALE_PAR_Gain2                                     0xF40EBFUL
#define ADSP_X_ALE_PAR_Gain3                                     0xF40EC0UL
#define ADSP_X_ALE_PAR_Gain4                                     0xF40EC1UL
#define ADSP_X_ALE_PAR_LEV_FilterGain_Exp                        0xF40EBDUL
#define ADSP_X_ALE_PAR_LEV_Gain1                                 0xF40EB9UL
#define ADSP_X_ALE_PAR_LEV_Gain2                                 0xF40EBBUL
#define ADSP_X_ALE_PAR_LEV_LS_Gain                               0xF40EB8UL
#define ADSP_X_ALE_PAR_LEV_OnOff                                 0xF40EADUL
#define ADSP_X_ALE_PAR_LEV_RelDecay1Gain                         0xF40EBAUL
#define ADSP_X_ALE_PAR_LEV_RelLevel1Thrs                         0xF40EBCUL
#define ADSP_X_ALE_PAR_LIM_Lower                                 0xF40EB6UL
#define ADSP_X_ALE_PAR_LIM_Threshold                             0xF40EB5UL
#define ADSP_X_ALE_PAR_LIM_Upper                                 0xF40EB7UL
#define ADSP_X_ALE_PAR_OnOff                                     0xF40EACUL
#define ADSP_X_ALE_PAR_OutS_Gain                                 0xF40EB0UL
#define ADSP_X_ALE_PAR_PassThrough_Gain                          0xF40EB1UL
#define ADSP_X_ALE_PAR_Reference_Level_Exp                       0xF40EAFUL
#define ADSP_X_AUB2_AGCMaxGain                                   0xF40441UL
#define ADSP_X_AUB2_InPntr                                       0xF4059FUL
#define ADSP_X_AUB2_Mode                                         0xF4043AUL
#define ADSP_X_AUB2_out1                                         0xF401CDUL
#define ADSP_X_AUB2_out2                                         0xF401CEUL
#define ADSP_X_AUB2_TargetLevel                                  0xF4043EUL
#define ADSP_X_BalFadOnOffPntr                                   0xF402A2UL
#define ADSP_X_BAU_Version1                                      0xF40003UL
#define ADSP_X_BAU_Version2                                      0xF40004UL
#define ADSP_X_CenterInPntr                                      0xF40570UL
#define ADSP_X_Chime_Cl_Out                                      0xF401C8UL
#define ADSP_X_Chime_Out                                         0xF401C7UL
#define ADSP_X_CompExp_C_InPntr                                  0xF405C1UL
#define ADSP_X_CompExp_F_InPntr                                  0xF405BFUL
#define ADSP_X_CompExp_InPntr                                    0xF4057AUL
#define ADSP_X_CompExp_OutC                                      0xF405F0UL
#define ADSP_X_CompExp_OutFL                                     0xF405ECUL
#define ADSP_X_CompExp_OutFR                                     0xF405EDUL
#define ADSP_X_CompExp_OutPL                                     0xF40171UL
#define ADSP_X_CompExp_OutPR                                     0xF40172UL
#define ADSP_X_CompExp_OutRL                                     0xF405EEUL
#define ADSP_X_CompExp_OutRR                                     0xF405EFUL
#define ADSP_X_CompExp_OutSw                                     0xF405F1UL
#define ADSP_X_CompExp_PonE                                      0xF401EDUL
#define ADSP_X_CompExp_R_InPntr                                  0xF405C0UL
#define ADSP_X_CompExp_Sw_InPntr                                 0xF405C2UL
#define ADSP_X_CompExp_switch                                    0xF401ECUL
#define ADSP_X_CompExp_Th                                        0xF401F2UL
#define ADSP_X_DCfilt_OutC                                       0xF40603UL
#define ADSP_X_DCfilt_OutFL                                      0xF405FFUL
#define ADSP_X_DCfilt_OutFR                                      0xF40600UL
#define ADSP_X_DCfilt_OutPL                                      0xF401A7UL
#define ADSP_X_DCfilt_OutPR                                      0xF401A8UL
#define ADSP_X_DCfilt_OutRL                                      0xF40601UL
#define ADSP_X_DCfilt_OutRR                                      0xF40602UL
#define ADSP_X_DCfilt_OutS2L                                     0xF401AFUL
#define ADSP_X_DCfilt_OutS2R                                     0xF401B0UL
#define ADSP_X_DCfilt_OutSL                                      0xF401A9UL
#define ADSP_X_DCfilt_OutSR                                      0xF401AAUL
#define ADSP_X_DCfilt_OutSw                                      0xF40604UL
#define ADSP_X_Delay_AD_InPntr                                   0xF405ABUL
#define ADSP_X_Delay_ADL_Out                                     0xF40181UL
#define ADSP_X_Delay_ADR_Out                                     0xF40182UL
#define ADSP_X_Delay_C_InPntr                                    0xF405A9UL
#define ADSP_X_Delay_F_InPntr                                    0xF405A7UL
#define ADSP_X_Delay_FL_Out                                      0xF4017BUL
#define ADSP_X_Delay_FR_Out                                      0xF4017CUL
#define ADSP_X_Delay_InitFlag                                    0xF40732UL
#define ADSP_X_Delay_Length1_In                                  0xF4072AUL
#define ADSP_X_Delay_Length2_In                                  0xF4072BUL
#define ADSP_X_Delay_Length3_In                                  0xF4072CUL
#define ADSP_X_Delay_Length4_In                                  0xF4072DUL
#define ADSP_X_Delay_Length5_In                                  0xF4072EUL
#define ADSP_X_Delay_Length6_In                                  0xF4072FUL
#define ADSP_X_Delay_Length7_In                                  0xF40730UL
#define ADSP_X_Delay_Length8_In                                  0xF40731UL
#define ADSP_X_Delay_R_InPntr                                    0xF405A8UL
#define ADSP_X_Delay_RL_Out                                      0xF4017DUL
#define ADSP_X_Delay_RR_Out                                      0xF4017EUL
#define ADSP_X_Delay_Start                                       0xF40729UL
#define ADSP_X_Delay_Sw_InPntr                                   0xF405AAUL
#define ADSP_X_Delay_SwL_Out                                     0xF4017FUL
#define ADSP_X_Delay_SwR_Out                                     0xF40180UL
#define ADSP_X_Dmph_Flag_Mask                                    0xF4001DUL
#define ADSP_X_Dmph_OutPL                                        0xF401ABUL
#define ADSP_X_Dmph_OutPR                                        0xF401ACUL
#define ADSP_X_Dmph_OutS2L                                       0xF401B1UL
#define ADSP_X_Dmph_OutS2R                                       0xF401B2UL
#define ADSP_X_Dmph_OutSL                                        0xF401ADUL
#define ADSP_X_Dmph_OutSR                                        0xF401AEUL
#define ADSP_X_Dmph_SPDIF_Mask                                   0xF4001CUL
#define ADSP_X_DwnMx_C_InPntr                                    0xF405AEUL
#define ADSP_X_DwnMx_F_InPntr                                    0xF405ACUL
#define ADSP_X_DwnMx_OutC                                        0xF401C1UL
#define ADSP_X_DwnMx_OutFL                                       0xF401BDUL
#define ADSP_X_DwnMx_OutFR                                       0xF401BEUL
#define ADSP_X_DwnMx_OutRL                                       0xF401BFUL
#define ADSP_X_DwnMx_OutRR                                       0xF401C0UL
#define ADSP_X_DwnMx_OutSw                                       0xF401C2UL
#define ADSP_X_DwnMx_R_InPntr                                    0xF405ADUL
#define ADSP_X_DwnMx_Sw_InPntr                                   0xF405AFUL
#define ADSP_X_EasyP_BackupIndex                                 0xF40095UL
#define ADSP_X_EasyP_Index                                       0xF40093UL
#define ADSP_X_EasyP_SubEntry                                    0xF40094UL
#define ADSP_X_Eq_OutFL                                          0xF40175UL
#define ADSP_X_Eq_OutFR                                          0xF40176UL
#define ADSP_X_Eq_OutRL                                          0xF40177UL
#define ADSP_X_Eq_OutRR                                          0xF40178UL
#define ADSP_X_Eq_OutSwL                                         0xF40179UL
#define ADSP_X_Eq_OutSwR                                         0xF4017AUL
#define ADSP_X_FastMute_FlagIOMask                               0xF4003CUL
#define ADSP_X_FCLim_FlgGenDSPIO_Polarity                        0xF40132UL
#define ADSP_X_FCLim_FlgGenFlagFR                                0xF40137UL
#define ADSP_X_FCLim_FlgGenFlagRS                                0xF4013AUL
#define ADSP_X_FCLim_FlgGenFlagS2                                0xF40127UL
#define ADSP_X_FCLim_FlgGenFlagSwL                               0xF40138UL
#define ADSP_X_FCLim_FlgGenFlagSwR                               0xF40139UL
#define ADSP_X_FCLim_FlgGenMaskFR                                0xF40133UL
#define ADSP_X_FCLim_FlgGenMaskRS                                0xF40136UL
#define ADSP_X_FCLim_FlgGenMaskS2                                0xF40126UL
#define ADSP_X_FCLim_FlgGenMaskSwL                               0xF40134UL
#define ADSP_X_FCLim_FlgGenMaskSwR                               0xF40135UL
#define ADSP_X_FCLim_Gain24bFR                                   0xF40129UL
#define ADSP_X_FCLim_Gain24bRS                                   0xF4012FUL
#define ADSP_X_FCLim_Gain24bS2                                   0xF40124UL
#define ADSP_X_FCLim_Gain24bSwL                                  0xF4012BUL
#define ADSP_X_FCLim_Gain24bSwR                                  0xF4012DUL
#define ADSP_X_FCLim_MinGainFR                                   0xF4012AUL
#define ADSP_X_FCLim_MinGainRS                                   0xF40130UL
#define ADSP_X_FCLim_MinGainS2                                   0xF40125UL
#define ADSP_X_FCLim_MinGainSwL                                  0xF4012CUL
#define ADSP_X_FCLim_MinGainSwR                                  0xF4012EUL
#define ADSP_X_FCLim_SCDGenMaskFR                                0xF4013BUL
#define ADSP_X_FCLim_SCDGenMaskRS                                0xF4013EUL
#define ADSP_X_FCLim_SCDGenMaskS2                                0xF40128UL
#define ADSP_X_FCLim_SCDGenMaskSwL                               0xF4013CUL
#define ADSP_X_FCLim_SCDGenMaskSwR                               0xF4013DUL
#define ADSP_X_FDACpntr                                          0xF402E3UL
#define ADSP_X_FInPntr                                           0xF4056DUL
#define ADSP_X_FrontOutL                                         0xF40167UL
#define ADSP_X_FrontOutR                                         0xF40168UL
#define ADSP_X_FSupInPntr                                        0xF4057DUL
#define ADSP_X_FVolInPntr                                        0xF40573UL
#define ADSP_X_GC1InPntr                                         0xF405BBUL
#define ADSP_X_GC1outL                                           0xF405E4UL
#define ADSP_X_GC1outR                                           0xF405E5UL
#define ADSP_X_GC2InPntr                                         0xF405BCUL
#define ADSP_X_GC2outL                                           0xF405E6UL
#define ADSP_X_GC2outR                                           0xF405E7UL
#define ADSP_X_GC3InPntr                                         0xF405BDUL
#define ADSP_X_GC3outL                                           0xF405E8UL
#define ADSP_X_GC3outR                                           0xF405E9UL
#define ADSP_X_GC4InPntr                                         0xF405BEUL
#define ADSP_X_GC4outL                                           0xF405EAUL
#define ADSP_X_GC4outR                                           0xF405EBUL
#define ADSP_X_GEq_C_InPntr                                      0xF4058EUL
#define ADSP_X_GEq_F_InPntr                                      0xF4058CUL
#define ADSP_X_GEq_OutFL                                         0xF40183UL
#define ADSP_X_GEq_OutFR                                         0xF40184UL
#define ADSP_X_GEq_OutL                                          0xF40183UL
#define ADSP_X_GEq_OutR                                          0xF40184UL
#define ADSP_X_GEq_OutRL                                         0xF40185UL
#define ADSP_X_GEq_OutRR                                         0xF40186UL
#define ADSP_X_GEq_OutSwL                                        0xF40187UL
#define ADSP_X_GEq_OutSwR                                        0xF40188UL
#define ADSP_X_GEq_R_InPntr                                      0xF4058DUL
#define ADSP_X_GEq_Sw_InPntr                                     0xF4058FUL
#define ADSP_X_GEqInPntr                                         0xF4058CUL
#define ADSP_X_GPadd_InPntr11                                    0xF405B0UL
#define ADSP_X_GPadd_InPntr12                                    0xF405B1UL
#define ADSP_X_GPadd_InPntr21                                    0xF405B2UL
#define ADSP_X_GPadd_InPntr22                                    0xF405B3UL
#define ADSP_X_GPadd_Out1                                        0xF405E0UL
#define ADSP_X_GPadd_Out2                                        0xF405E1UL
#define ADSP_X_GPC48_10L_InPntr                                  0xF40E5FUL
#define ADSP_X_GPC48_10R_InPntr                                  0xF40E60UL
#define ADSP_X_GPC48_11L_InPntr                                  0xF40E61UL
#define ADSP_X_GPC48_11R_InPntr                                  0xF40E62UL
#define ADSP_X_GPC48_12L_InPntr                                  0xF40E63UL
#define ADSP_X_GPC48_12R_InPntr                                  0xF40E64UL
#define ADSP_X_GPC48_1L_InPntr                                   0xF40E4DUL
#define ADSP_X_GPC48_1R_InPntr                                   0xF40E4EUL
#define ADSP_X_GPC48_2L_InPntr                                   0xF40E4FUL
#define ADSP_X_GPC48_2R_InPntr                                   0xF40E50UL
#define ADSP_X_GPC48_3L_InPntr                                   0xF40E51UL
#define ADSP_X_GPC48_3R_InPntr                                   0xF40E52UL
#define ADSP_X_GPC48_4L_InPntr                                   0xF40E53UL
#define ADSP_X_GPC48_4R_InPntr                                   0xF40E54UL
#define ADSP_X_GPC48_5L_InPntr                                   0xF40E55UL
#define ADSP_X_GPC48_5R_InPntr                                   0xF40E56UL
#define ADSP_X_GPC48_6L_InPntr                                   0xF40E57UL
#define ADSP_X_GPC48_6R_InPntr                                   0xF40E58UL
#define ADSP_X_GPC48_7L_InPntr                                   0xF40E59UL
#define ADSP_X_GPC48_7R_InPntr                                   0xF40E5AUL
#define ADSP_X_GPC48_8L_InPntr                                   0xF40E5BUL
#define ADSP_X_GPC48_8R_InPntr                                   0xF40E5CUL
#define ADSP_X_GPC48_9L_InPntr                                   0xF40E5DUL
#define ADSP_X_GPC48_9R_InPntr                                   0xF40E5EUL
#define ADSP_X_GPC48_NrOfGPC                                     0xF40E4CUL
#define ADSP_X_GPC48_Out10L                                      0xF40E77UL
#define ADSP_X_GPC48_Out10R                                      0xF40E78UL
#define ADSP_X_GPC48_Out11L                                      0xF40E79UL
#define ADSP_X_GPC48_Out11R                                      0xF40E7AUL
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
#define ADSP_X_GPFastMute_Out7L                                  0xF40435UL
#define ADSP_X_GPFastMute_Out7R                                  0xF40436UL
#define ADSP_X_GPFastMute_Out8L                                  0xF40437UL
#define ADSP_X_GPFastMute_Out8R                                  0xF40438UL
#define ADSP_X_GPFastMute1_Inpntr                                0xF40421UL
#define ADSP_X_GPFastMute2_Inpntr                                0xF40422UL
#define ADSP_X_GPFastMute3_Inpntr                                0xF40423UL
#define ADSP_X_GPFastMute4_Inpntr                                0xF40424UL
#define ADSP_X_GPFastMute5_Inpntr                                0xF40425UL
#define ADSP_X_GPFastMute6_Inpntr                                0xF40426UL
#define ADSP_X_GPFastMute7_Inpntr                                0xF40427UL
#define ADSP_X_GPFastMute8_Inpntr                                0xF40428UL
#define ADSP_X_Gsa_Bar321                                        0xF40EABUL
#define ADSP_X_Gsa_Bar654                                        0xF40EAAUL
#define ADSP_X_Gsa_Bar987                                        0xF40EA9UL
#define ADSP_X_Gsa_InPntr                                        0xF405C7UL
#define ADSP_X_Gsa_Thresh1                                       0xF40E95UL
#define ADSP_X_Gsa_Thresh2                                       0xF40E96UL
#define ADSP_X_Gsa_Thresh3                                       0xF40E97UL
#define ADSP_X_Gsa_Thresh4                                       0xF40E98UL
#define ADSP_X_Gsa_Thresh5                                       0xF40E99UL
#define ADSP_X_Gsa_Thresh6                                       0xF40E9AUL
#define ADSP_X_Gsa_Thresh7                                       0xF40E9BUL
#define ADSP_X_Gsa_Thresh8                                       0xF40E9CUL
#define ADSP_X_HIIS0Outpntr                                      0xF402AEUL
#define ADSP_X_HIIS1Outpntr                                      0xF402AFUL
#define ADSP_X_HIIS2Outpntr                                      0xF402B0UL
#define ADSP_X_HIIS3Outpntr                                      0xF402B1UL
#define ADSP_X_HIIS4InL                                          0xF400BAUL
#define ADSP_X_HIIS4InR                                          0xF400BBUL
#define ADSP_X_HIIS5InL                                          0xF400BCUL
#define ADSP_X_HIIS5InR                                          0xF400BDUL
#define ADSP_X_HIIS6InL                                          0xF400B4UL
#define ADSP_X_HIIS6InR                                          0xF400B5UL
#define ADSP_X_HIIS7InL                                          0xF400B6UL
#define ADSP_X_HIIS7InR                                          0xF400B7UL
#define ADSP_X_HIIS8InL                                          0xF400B8UL
#define ADSP_X_HIIS8InR                                          0xF400B9UL
#define ADSP_X_IBblnd_An2DigRate                                 0xF402E6UL
#define ADSP_X_IBblnd_AnInPntr                                   0xF40564UL
#define ADSP_X_IBblnd_AnInPntrS                                  0xF40566UL
#define ADSP_X_IBblnd_AnInPntrS2                                 0xF40567UL
#define ADSP_X_IBblnd_Dig2AnRate                                 0xF402E7UL
#define ADSP_X_IBblnd_DigInPntr                                  0xF40565UL
#define ADSP_X_IBblnd_Flag_IOFMask                               0xF402EBUL
#define ADSP_X_IBblnd_OutL                                       0xF40161UL
#define ADSP_X_IBblnd_OutR                                       0xF40162UL
#define ADSP_X_IBblnd_OutS2L                                     0xF40165UL
#define ADSP_X_IBblnd_OutS2R                                     0xF40166UL
#define ADSP_X_IBblnd_OutSL                                      0xF40163UL
#define ADSP_X_IBblnd_OutSR                                      0xF40164UL
#define ADSP_X_IIS1FrontPntr                                     0xF402DAUL
#define ADSP_X_IIS1RearPntr                                      0xF402DBUL
#define ADSP_X_IIS1SubWCPntr                                     0xF402DCUL
#define ADSP_X_IPC_BAU2ADV_OutEXTL                               0xF401DFUL
#define ADSP_X_IPC_BAU2ADV_OutEXTR                               0xF401E0UL
#define ADSP_X_IPC_BAU2ADV_OutFL                                 0xF401D1UL
#define ADSP_X_IPC_BAU2ADV_OutFR                                 0xF401D2UL
#define ADSP_X_IPC_BAU2ADV_OutHDRL                               0xF401DDUL
#define ADSP_X_IPC_BAU2ADV_OutHDRR                               0xF401DEUL
#define ADSP_X_IPC_BAU2ADV_OutN                                  0xF401DBUL
#define ADSP_X_IPC_BAU2ADV_OutRL                                 0xF401D3UL
#define ADSP_X_IPC_BAU2ADV_OutRR                                 0xF401D4UL
#define ADSP_X_IPC_BAU2ADV_OutS1L                                0xF401D7UL
#define ADSP_X_IPC_BAU2ADV_OutS1R                                0xF401D8UL
#define ADSP_X_IPC_BAU2ADV_OutS2L                                0xF401D9UL
#define ADSP_X_IPC_BAU2ADV_OutS2R                                0xF401DAUL
#define ADSP_X_IPC_BAU2ADV_OutSwL                                0xF401D5UL
#define ADSP_X_IPC_BAU2ADV_OutSwR                                0xF401D6UL
#define ADSP_X_IPC_BAU2ADV_OutT                                  0xF401DCUL
#define ADSP_X_IPC_BAU2ADV_pCStr                                 0xF405D1UL
#define ADSP_X_IPC_BAU2ADV_pEXTStr                               0xF405D8UL
#define ADSP_X_IPC_BAU2ADV_pFStr                                 0xF405CFUL
#define ADSP_X_IPC_BAU2ADV_pHDRStr                               0xF405D7UL
#define ADSP_X_IPC_BAU2ADV_pNStr                                 0xF405D5UL
#define ADSP_X_IPC_BAU2ADV_pRStr                                 0xF405D0UL
#define ADSP_X_IPC_BAU2ADV_pS1Str                                0xF405D3UL
#define ADSP_X_IPC_BAU2ADV_pS2Str                                0xF405D4UL
#define ADSP_X_IPC_BAU2ADV_pSwStr                                0xF405D2UL
#define ADSP_X_IPC_BAU2ADV_pTStr                                 0xF405D6UL
#define ADSP_X_Loudf_DynSwtch                                    0xF40412UL
#define ADSP_X_Loudf_HldThrshB                                   0xF40418UL
#define ADSP_X_Loudf_HldThrshT                                   0xF4041DUL
#define ADSP_X_Loudf_InPntr                                      0xF40592UL
#define ADSP_X_Loudf_LevInPntr                                   0xF4041FUL
#define ADSP_X_Loudf_OutFL                                       0xF4018FUL
#define ADSP_X_Loudf_OutFR                                       0xF40190UL
#define ADSP_X_Loudf_OutL                                        0xF4018FUL
#define ADSP_X_Loudf_OutR                                        0xF40190UL
#define ADSP_X_Loudf_OutRL                                       0xF40191UL
#define ADSP_X_Loudf_OutRR                                       0xF40192UL
#define ADSP_X_Loudf_OutSwL                                      0xF40193UL
#define ADSP_X_Loudf_OutSwR                                      0xF40194UL
#define ADSP_X_Loudf6_InPntr                                     0xF40593UL
#define ADSP_X_MkSubwLeft                                        0xF40173UL
#define ADSP_X_MkSubwRight                                       0xF40174UL
#define ADSP_X_Mute_outDac                                       0xF4003FUL
#define ADSP_X_Mute_outGC1                                       0xF40083UL
#define ADSP_X_Mute_outGC2                                       0xF40086UL
#define ADSP_X_Mute_outGC3                                       0xF40089UL
#define ADSP_X_Mute_outGC4                                       0xF4008CUL
#define ADSP_X_Mute_outN                                         0xF4006DUL
#define ADSP_X_Mute_outP                                         0xF40058UL
#define ADSP_X_Mute_outS                                         0xF40068UL
#define ADSP_X_Mute_outS2                                        0xF4007AUL
#define ADSP_X_Mute_outT                                         0xF40072UL
#define ADSP_X_Mute_StpAttDac                                    0xF4003DUL
#define ADSP_X_Mute_StpAttGC1                                    0xF40081UL
#define ADSP_X_Mute_StpAttGC2                                    0xF40084UL
#define ADSP_X_Mute_StpAttGC3                                    0xF40087UL
#define ADSP_X_Mute_StpAttGC4                                    0xF4008AUL
#define ADSP_X_Mute_StpAttN                                      0xF4006BUL
#define ADSP_X_Mute_StpAttP                                      0xF40056UL
#define ADSP_X_Mute_StpAttS                                      0xF40066UL
#define ADSP_X_Mute_StpAttS2                                     0xF40078UL
#define ADSP_X_Mute_StpAttT                                      0xF40070UL
#define ADSP_X_Mute_StpRelDac                                    0xF4003EUL
#define ADSP_X_Mute_StpRelGC1                                    0xF40082UL
#define ADSP_X_Mute_StpRelGC2                                    0xF40085UL
#define ADSP_X_Mute_StpRelGC3                                    0xF40088UL
#define ADSP_X_Mute_StpRelGC4                                    0xF4008BUL
#define ADSP_X_Mute_StpRelN                                      0xF4006CUL
#define ADSP_X_Mute_StpRelP                                      0xF40057UL
#define ADSP_X_Mute_StpRelS                                      0xF40067UL
#define ADSP_X_Mute_StpRelS2                                     0xF40079UL
#define ADSP_X_Mute_StpRelT                                      0xF40071UL
#define ADSP_X_MuteSix_outFL                                     0xF4005BUL
#define ADSP_X_MuteSix_outFR                                     0xF4005CUL
#define ADSP_X_MuteSix_outRL                                     0xF4005DUL
#define ADSP_X_MuteSix_outRR                                     0xF4005EUL
#define ADSP_X_MuteSix_outSwL                                    0xF4005FUL
#define ADSP_X_MuteSix_outSwR                                    0xF40060UL
#define ADSP_X_MuteSix_StpAtt                                    0xF40059UL
#define ADSP_X_MuteSix_StpRel                                    0xF4005AUL
#define ADSP_X_Navb4EQ                                           0xF401A3UL
#define ADSP_X_NavBackInPntr                                     0xF40577UL
#define ADSP_X_NavOut                                            0xF4015DUL
#define ADSP_X_NChanSelPntr                                      0xF4056AUL
#define ADSP_X_NG_OutL                                           0xF401C9UL
#define ADSP_X_NG_OutR                                           0xF401CAUL
#define ADSP_X_PChan_C_SelPntr                                   0xF40562UL
#define ADSP_X_PChan_F_SelPntr                                   0xF40560UL
#define ADSP_X_PChan_R_SelPntr                                   0xF40561UL
#define ADSP_X_PChan_Sw_SelPntr                                  0xF40563UL
#define ADSP_X_PChannelMode_OutL                                 0xF401CFUL
#define ADSP_X_PChannelMode_OutR                                 0xF401D0UL
#define ADSP_X_PChanSelPntr                                      0xF4055DUL
#define ADSP_X_PCHIME_AngleIncr_LFO                              0xF40FA6UL
#define ADSP_X_PCHIME_ControlStatusReg                           0xF40FB5UL
#define ADSP_X_PCHIME_Env1_AttackIncr                            0xF40FA8UL
#define ADSP_X_PCHIME_Env1_DelaySamples                          0xF40FA7UL
#define ADSP_X_PCHIME_Env1_SustainSamples                        0xF40FA9UL
#define ADSP_X_PCHIME_Env2_AttackIncr                            0xF40FABUL
#define ADSP_X_PCHIME_Env2_DelaySamples                          0xF40FAAUL
#define ADSP_X_PCHIME_Env2_SustainSamples                        0xF40FACUL
#define ADSP_X_PCHIME_Env3_AttackIncr                            0xF40FAEUL
#define ADSP_X_PCHIME_Env3_DelaySamples                          0xF40FADUL
#define ADSP_X_PCHIME_Env3_SustainSamples                        0xF40FAFUL
#define ADSP_X_PCHIME_Env4_AttackIncr                            0xF40FB1UL
#define ADSP_X_PCHIME_Env4_DelaySamples                          0xF40FB0UL
#define ADSP_X_PCHIME_Env4_SustainSamples                        0xF40FB2UL
#define ADSP_X_PCHIME_NrRepetitions                              0xF40FB3UL
#define ADSP_X_PCHIME_out                                        0xF405DEUL
#define ADSP_X_PCHIME_RepeatSamples                              0xF40FB4UL
#define ADSP_X_PCHIME2_AngleIncr_LFO                             0xF40D86UL
#define ADSP_X_PCHIME2_ControlStatusReg                          0xF40D95UL
#define ADSP_X_PCHIME2_Env1_AttackIncr                           0xF40D88UL
#define ADSP_X_PCHIME2_Env1_DelaySamples                         0xF40D87UL
#define ADSP_X_PCHIME2_Env1_SustainSamples                       0xF40D89UL
#define ADSP_X_PCHIME2_Env2_AttackIncr                           0xF40D8BUL
#define ADSP_X_PCHIME2_Env2_DelaySamples                         0xF40D8AUL
#define ADSP_X_PCHIME2_Env2_SustainSamples                       0xF40D8CUL
#define ADSP_X_PCHIME2_Env3_AttackIncr                           0xF40D8EUL
#define ADSP_X_PCHIME2_Env3_DelaySamples                         0xF40D8DUL
#define ADSP_X_PCHIME2_Env3_SustainSamples                       0xF40D8FUL
#define ADSP_X_PCHIME2_Env4_AttackIncr                           0xF40D91UL
#define ADSP_X_PCHIME2_Env4_DelaySamples                         0xF40D90UL
#define ADSP_X_PCHIME2_Env4_SustainSamples                       0xF40D92UL
#define ADSP_X_PCHIME2_NrRepetitions                             0xF40D93UL
#define ADSP_X_PCHIME2_out                                       0xF405DFUL
#define ADSP_X_PCHIME2_RepeatSamples                             0xF40D94UL
#define ADSP_X_PDC2_Out                                          0xF404DAUL
#define ADSP_X_Phonb4EQ                                          0xF401A4UL
#define ADSP_X_PhonBackInPntr                                    0xF40578UL
#define ADSP_X_PhonOut                                           0xF4015EUL
#define ADSP_X_PMC_energyFilterCoeff1X                           0xF40DD1UL
#define ADSP_X_PMC_energyFilterCoeff2X                           0xF40DD2UL
#define ADSP_X_PMC_OutC                                          0xF40199UL
#define ADSP_X_PMC_OutFL                                         0xF40195UL
#define ADSP_X_PMC_OutFR                                         0xF40196UL
#define ADSP_X_PMC_OutLFE                                        0xF4019AUL
#define ADSP_X_PMC_OutRL                                         0xF40197UL
#define ADSP_X_PMC_OutRR                                         0xF40198UL
#define ADSP_X_PMC_par_centerWidthX                              0xF40DCCUL
#define ADSP_X_PMC_par_correlationX                              0xF40DCEUL
#define ADSP_X_PMC_par_decorrelationX                            0xF40DCDUL
#define ADSP_X_PMC_par_frontBackBalanceX                         0xF40DCAUL
#define ADSP_X_PMC_par_leftRightBalanceX                         0xF40DC9UL
#define ADSP_X_PMC_par_matrixInversionX                          0xF40DD0UL
#define ADSP_X_PMC_par_minIccLimitX                              0xF40DCFUL
#define ADSP_X_PMC_par_surroundEffectX                           0xF40DCBUL
#define ADSP_X_PMC_pIn                                           0xF40596UL
#define ADSP_X_PProcSelPntr                                      0xF40568UL
#define ADSP_X_PrimInModePntr                                    0xF405DAUL
#define ADSP_X_PToneControl_InPntr                               0xF40590UL
#define ADSP_X_PToneControl6_InPntr                              0xF40591UL
#define ADSP_X_PVol_InPntr                                       0xF40571UL
#define ADSP_X_PVol6_InPntr                                      0xF40572UL
#define ADSP_X_QPD_COUNTMAX1                                     0xF40121UL
#define ADSP_X_QPD_COUNTMAX2                                     0xF40123UL
#define ADSP_X_QPD_InPntr11                                      0xF405B4UL
#define ADSP_X_QPD_InPntr12                                      0xF405B5UL
#define ADSP_X_QPD_InPntr21                                      0xF405B6UL
#define ADSP_X_QPD_InPntr22                                      0xF405B7UL
#define ADSP_X_QPD_MaxIn1                                        0xF4011EUL
#define ADSP_X_QPD_MaxIn2                                        0xF4011FUL
#define ADSP_X_QPD_NonAverPeak1                                  0xF401C4UL
#define ADSP_X_QPD_NonAverPeak2                                  0xF401C6UL
#define ADSP_X_QPD_Peak1                                         0xF401C3UL
#define ADSP_X_QPD_Peak2                                         0xF401C5UL
#define ADSP_X_RDACpntr                                          0xF402E4UL
#define ADSP_X_RearOutL                                          0xF40169UL
#define ADSP_X_RearOutR                                          0xF4016AUL
#define ADSP_X_RInPntr                                           0xF4056EUL
#define ADSP_X_RSupInPntr                                        0xF4057EUL
#define ADSP_X_RVolInPntr                                        0xF40574UL
#define ADSP_X_S2ChanSelPntr                                     0xF4055FUL
#define ADSP_X_S2ProcSelPntr                                     0xF4056CUL
#define ADSP_X_S2SupInPntr                                       0xF4058AUL
#define ADSP_X_S2VolInPntr                                       0xF40579UL
#define ADSP_X_SCD_InPntr00                                      0xF405C9UL
#define ADSP_X_SCD_InPntr01                                      0xF405CAUL
#define ADSP_X_SCD_InPntr1                                       0xF405CBUL
#define ADSP_X_SCD_InPntr2                                       0xF405CCUL
#define ADSP_X_SCD_InPntr3                                       0xF405CDUL
#define ADSP_X_SCD_InPntr4                                       0xF405CEUL
#define ADSP_X_SCD_Peak0                                         0xF406C3UL
#define ADSP_X_SCD_Peak1                                         0xF406C4UL
#define ADSP_X_SCD_Peak2                                         0xF406C5UL
#define ADSP_X_SCD_Peak3                                         0xF406C6UL
#define ADSP_X_SCD_Peak4                                         0xF406CBUL
#define ADSP_X_SCD_SWFlags                                       0xF405F8UL
#define ADSP_X_SCD_Thresh0                                       0xF406C7UL
#define ADSP_X_SCD_Thresh1                                       0xF406C8UL
#define ADSP_X_SCD_Thresh2                                       0xF406C9UL
#define ADSP_X_SCD_Thresh3                                       0xF406CAUL
#define ADSP_X_SCD_Thresh4                                       0xF406CCUL
#define ADSP_X_SChanSelPntr                                      0xF4055EUL
#define ADSP_X_SCLP_C_Am                                         0xF406D8UL
#define ADSP_X_SCLP_C_c                                          0xF406D7UL
#define ADSP_X_SCLP_C_M                                          0xF406D6UL
#define ADSP_X_SCLP_C_T                                          0xF406D5UL
#define ADSP_X_SCLP_F_Am                                         0xF406D0UL
#define ADSP_X_SCLP_F_c                                          0xF406CFUL
#define ADSP_X_SCLP_F_M                                          0xF406CEUL
#define ADSP_X_SCLP_F_T                                          0xF406CDUL
#define ADSP_X_SCLP_InPntr                                       0xF405B8UL
#define ADSP_X_SCLP_OutC                                         0xF405FDUL
#define ADSP_X_SCLP_OutFL                                        0xF405F9UL
#define ADSP_X_SCLP_OutFR                                        0xF405FAUL
#define ADSP_X_SCLP_OutRL                                        0xF405FBUL
#define ADSP_X_SCLP_OutRR                                        0xF405FCUL
#define ADSP_X_SCLP_OutSw                                        0xF405FEUL
#define ADSP_X_SCLP_R_Am                                         0xF406D4UL
#define ADSP_X_SCLP_R_c                                          0xF406D3UL
#define ADSP_X_SCLP_R_M                                          0xF406D2UL
#define ADSP_X_SCLP_R_T                                          0xF406D1UL
#define ADSP_X_SCLP_Sw_Am                                        0xF406DCUL
#define ADSP_X_SCLP_Sw_c                                         0xF406DBUL
#define ADSP_X_SCLP_Sw_M                                         0xF406DAUL
#define ADSP_X_SCLP_Sw_T                                         0xF406D9UL
#define ADSP_X_Sec2OutL                                          0xF4016FUL
#define ADSP_X_Sec2OutR                                          0xF40170UL
#define ADSP_X_SecOutL                                           0xF4016DUL
#define ADSP_X_SecOutR                                           0xF4016EUL
#define ADSP_X_SinGen_OutL                                       0xF401C9UL
#define ADSP_X_SinGen_OutR                                       0xF401CAUL
#define ADSP_X_SPDIF0Outpntr                                     0xF402ACUL
#define ADSP_X_SPDIF1Outpntr                                     0xF402ADUL
#define ADSP_X_SProcSelPntr                                      0xF40569UL
#define ADSP_X_SRC0InC                                           0xF400A2UL
#define ADSP_X_SRC0InFL                                          0xF4009EUL
#define ADSP_X_SRC0InFR                                          0xF4009FUL
#define ADSP_X_SRC0InRL                                          0xF400A0UL
#define ADSP_X_SRC0InRR                                          0xF400A1UL
#define ADSP_X_SRC0InSw                                          0xF400A3UL
#define ADSP_X_SRC0Outpntr                                       0xF402E2UL
#define ADSP_X_SRC1InL                                           0xF400A4UL
#define ADSP_X_SRC1InR                                           0xF400A5UL
#define ADSP_X_SRC2InL                                           0xF400A6UL
#define ADSP_X_SRC2InR                                           0xF400A7UL
#define ADSP_X_SRC3InL                                           0xF400A8UL
#define ADSP_X_SRC3InR                                           0xF400A9UL
#define ADSP_X_SRC4InL                                           0xF400AAUL
#define ADSP_X_SRC4InR                                           0xF400ABUL
#define ADSP_X_SRC5InL                                           0xF400ACUL
#define ADSP_X_SRC5InR                                           0xF400ADUL
#define ADSP_X_SrcScal6_C_InPntr                                 0xF405C5UL
#define ADSP_X_SrcScal6_F_InPntr                                 0xF405C3UL
#define ADSP_X_SrcScal6_R_InPntr                                 0xF405C4UL
#define ADSP_X_SrcScal6_Sw_InPntr                                0xF405C6UL
#define ADSP_X_SrcSw_DmphModPntrA                                0xF4008DUL
#define ADSP_X_SrcSw_DmphModPntrB                                0xF4008EUL
#define ADSP_X_SrcSw_DmphModPntrC                                0xF4008FUL
#define ADSP_X_SrcSw_OrDigSrcSelMask                             0xF40092UL
#define ADSP_X_SSupInPntr                                        0xF40580UL
#define ADSP_X_SubwInPntr                                        0xF4056FUL
#define ADSP_X_Sup_ChiInPntr                                     0xF40586UL
#define ADSP_X_Sup_ExtInPntr                                     0xF40584UL
#define ADSP_X_Sup_NInPntr                                       0xF40582UL
#define ADSP_X_Sup_PChiInPntr                                    0xF40585UL
#define ADSP_X_Sup_PDC2InPntr                                    0xF40581UL
#define ADSP_X_Sup_TInPntr                                       0xF40583UL
#define ADSP_X_SupPosB_C_InPntr                                  0xF40599UL
#define ADSP_X_SupPosB_C_Out                                     0xF4019FUL
#define ADSP_X_SupPosB_F_InPntr                                  0xF40597UL
#define ADSP_X_SupPosB_FL_InPntr                                 0xF4059BUL
#define ADSP_X_SupPosB_FL_Out                                    0xF4019BUL
#define ADSP_X_SupPosB_FR_InPntr                                 0xF4059CUL
#define ADSP_X_SupPosB_FR_Out                                    0xF4019CUL
#define ADSP_X_SupPosB_R_InPntr                                  0xF40598UL
#define ADSP_X_SupPosB_RL_InPntr                                 0xF4059DUL
#define ADSP_X_SupPosB_RL_Out                                    0xF4019DUL
#define ADSP_X_SupPosB_RR_InPntr                                 0xF4059EUL
#define ADSP_X_SupPosB_RR_Out                                    0xF4019EUL
#define ADSP_X_SupPosB_Sw_InPntr                                 0xF4059AUL
#define ADSP_X_SupPosB_Sw_Out                                    0xF401A0UL
#define ADSP_X_SVolInPntr                                        0xF40576UL
#define ADSP_X_SWDACpntr                                         0xF402E5UL
#define ADSP_X_SwFInPntr                                         0xF4057BUL
#define ADSP_X_SwOutL                                            0xF4016BUL
#define ADSP_X_SwOutR                                            0xF4016CUL
#define ADSP_X_SwRInPntr                                         0xF4057CUL
#define ADSP_X_SwSupInPntr                                       0xF4057FUL
#define ADSP_X_SwVolInPntr                                       0xF40575UL
#define ADSP_X_TChanSelPntr                                      0xF4056BUL
#define ADSP_X_TDM0In0                                           0xF400BEUL
#define ADSP_X_TDM0In1                                           0xF400BFUL
#define ADSP_X_TDM0In10                                          0xF400C8UL
#define ADSP_X_TDM0In11                                          0xF400C9UL
#define ADSP_X_TDM0In12                                          0xF400CAUL
#define ADSP_X_TDM0In13                                          0xF400CBUL
#define ADSP_X_TDM0In14                                          0xF400CCUL
#define ADSP_X_TDM0In15                                          0xF400CDUL
#define ADSP_X_TDM0In2                                           0xF400C0UL
#define ADSP_X_TDM0In3                                           0xF400C1UL
#define ADSP_X_TDM0In4                                           0xF400C2UL
#define ADSP_X_TDM0In5                                           0xF400C3UL
#define ADSP_X_TDM0In6                                           0xF400C4UL
#define ADSP_X_TDM0In7                                           0xF400C5UL
#define ADSP_X_TDM0In8                                           0xF400C6UL
#define ADSP_X_TDM0In9                                           0xF400C7UL
#define ADSP_X_TDM0Out1pntr                                      0xF402B2UL
#define ADSP_X_TDM0Out2pntr                                      0xF402B3UL
#define ADSP_X_TDM0Out3pntr                                      0xF402B4UL
#define ADSP_X_TDM0Out4pntr                                      0xF402B5UL
#define ADSP_X_TDM0Out5pntr                                      0xF402B6UL
#define ADSP_X_TDM0Out6pntr                                      0xF402B7UL
#define ADSP_X_TDM0Out7pntr                                      0xF402B8UL
#define ADSP_X_TDM0Out8pntr                                      0xF402B9UL
#define ADSP_X_TDM1In0                                           0xF400CEUL
#define ADSP_X_TDM1In1                                           0xF400CFUL
#define ADSP_X_TDM1In10                                          0xF400D8UL
#define ADSP_X_TDM1In11                                          0xF400D9UL
#define ADSP_X_TDM1In12                                          0xF400DAUL
#define ADSP_X_TDM1In13                                          0xF400DBUL
#define ADSP_X_TDM1In14                                          0xF400DCUL
#define ADSP_X_TDM1In15                                          0xF400DDUL
#define ADSP_X_TDM1In2                                           0xF400D0UL
#define ADSP_X_TDM1In3                                           0xF400D1UL
#define ADSP_X_TDM1In4                                           0xF400D2UL
#define ADSP_X_TDM1In5                                           0xF400D3UL
#define ADSP_X_TDM1In6                                           0xF400D4UL
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
#define ADSP_X_TDM5In6                                           0xF40114UL
#define ADSP_X_TDM5In7                                           0xF40115UL
#define ADSP_X_TDM5In8                                           0xF40116UL
#define ADSP_X_TDM5In9                                           0xF40117UL
#define ADSP_X_TDM5Out1pntr                                      0xF402DAUL
#define ADSP_X_TDM5Out2pntr                                      0xF402DBUL
#define ADSP_X_TDM5Out3pntr                                      0xF402DCUL
#define ADSP_X_TDM5Out4pntr                                      0xF402DDUL
#define ADSP_X_TDM5Out5pntr                                      0xF402DEUL
#define ADSP_X_TDM5Out6pntr                                      0xF402DFUL
#define ADSP_X_TDM5Out7pntr                                      0xF402E0UL
#define ADSP_X_TDM5Out8pntr                                      0xF402E1UL
#define ADSP_X_ToneOutFL                                         0xF40189UL
#define ADSP_X_ToneOutFR                                         0xF4018AUL
#define ADSP_X_ToneOutPL                                         0xF40189UL
#define ADSP_X_ToneOutPR                                         0xF4018AUL
#define ADSP_X_ToneOutRL                                         0xF4018BUL
#define ADSP_X_ToneOutRR                                         0xF4018CUL
#define ADSP_X_ToneOutSwL                                        0xF4018DUL
#define ADSP_X_ToneOutSwR                                        0xF4018EUL
#define ADSP_X_Tsq_addmul_Bk                                     0xF404FEUL
#define ADSP_X_Tsq_AddnlBoost                                    0xF4002FUL
#define ADSP_X_Tsq_ArLinStpA_Bk                                  0xF404F5UL
#define ADSP_X_Tsq_ArRelCoef                                     0xF404E4UL
#define ADSP_X_Tsq_ArRelCoef_Bk                                  0xF404F6UL
#define ADSP_X_Tsq_ChangeThreshold                               0xF40500UL
#define ADSP_X_Tsq_Cntr0                                         0xF404E8UL
#define ADSP_X_Tsq_CrosFStp_Bk                                   0xF404F4UL
#define ADSP_X_Tsq_DecayThreshold                                0xF40501UL
#define ADSP_X_Tsq_repeate                                       0xF404EBUL
#define ADSP_X_Tsq_repeate_Bk                                    0xF404F7UL
#define ADSP_X_Tsq_T1_Bk                                         0xF404FAUL
#define ADSP_X_Tsq_T2_Bk                                         0xF404FBUL
#define ADSP_X_Tsq_T3_Bk                                         0xF404FCUL
#define ADSP_X_Tsq_T4_Bk                                         0xF404FDUL
#define ADSP_X_Tsq_TA_Bk                                         0xF404F8UL
#define ADSP_X_Tsq_TB_Bk                                         0xF404F9UL
#define ADSP_X_UpdatC_NrOfCoeff                                  0xF40093UL
#define ADSP_X_Vol_Boost12dB                                     0xF4004DUL
#define ADSP_X_Vol_OneOverMaxBoostP                              0xF40050UL
#define ADSP_X_Vol_OneOverMaxBoostS                              0xF40053UL
#define ADSP_X_Vol_OneOverMaxBoostS2                             0xF4007CUL
#define ADSP_X_Vol_OutFL                                         0xF40155UL
#define ADSP_X_Vol_OutFR                                         0xF40156UL
#define ADSP_X_Vol_OutPL                                         0xF4014FUL
#define ADSP_X_Vol_OutPR                                         0xF40150UL
#define ADSP_X_Vol_OutRL                                         0xF40157UL
#define ADSP_X_Vol_OutRR                                         0xF40158UL
#define ADSP_X_Vol_OutS2L                                        0xF4015FUL
#define ADSP_X_Vol_OutS2R                                        0xF40160UL
#define ADSP_X_Vol_OutScalS2L                                    0xF401A5UL
#define ADSP_X_Vol_OutScalS2R                                    0xF401A6UL
#define ADSP_X_Vol_OutScalSL                                     0xF401A1UL
#define ADSP_X_Vol_OutScalSR                                     0xF401A2UL
#define ADSP_X_Vol_OutSL                                         0xF4015BUL
#define ADSP_X_Vol_OutSR                                         0xF4015CUL
#define ADSP_X_Vol_OutSwL                                        0xF40159UL
#define ADSP_X_Vol_OutSwR                                        0xF4015AUL
#define ADSP_X_Vol_SrcScalOutC                                   0xF405F6UL
#define ADSP_X_Vol_SrcScalOutFL                                  0xF405F2UL
#define ADSP_X_Vol_SrcScalOutFR                                  0xF405F3UL
#define ADSP_X_Vol_SrcScalOutRL                                  0xF405F4UL
#define ADSP_X_Vol_SrcScalOutRR                                  0xF405F5UL
#define ADSP_X_Vol_SrcScalOutSw                                  0xF405F7UL
#define ADSP_X_Vol_UnscalBMTGEQP                                 0xF40051UL
#define ADSP_X_VolMain1P_OutFL                                   0xF4014FUL
#define ADSP_X_VolMain1P_OutFR                                   0xF40150UL
#define ADSP_X_VolMain1P_OutRL                                   0xF40151UL
#define ADSP_X_VolMain1P_OutRR                                   0xF40152UL
#define ADSP_X_VolMain1P_OutSwL                                  0xF40153UL
#define ADSP_X_VolMain1P_OutSwR                                  0xF40154UL
#define ADSP_X_WavTab_Control                                    0xF40629UL
#define ADSP_X_WavTab_FlagIOFMask                                0xF40637UL
#define ADSP_X_WavTab_Pointer                                    0xF4062BUL
#define ADSP_X_WavTab_Ram_BuffEnd                                0xF40929UL
#define ADSP_X_WavTab_Ram_BuffStart                              0xF4074BUL
#define ADSP_X_WavTab_TacEndPntr                                 0xF40633UL
#define ADSP_X_WavTab_TacStartPntr                               0xF40632UL
#define ADSP_X_WavTab_TicEndPntr                                 0xF40631UL
#define ADSP_X_WavTab_TicStartPntr                               0xF40630UL
#define ADSP_X_WavTab_UseIOFlag                                  0xF40635UL
#define ADSP_X_WavTab_UseRamFlag                                 0xF40634UL
#define ADSP_X_ZeroSig0                                          0xF4013FUL
#define ADSP_X_ZeroSig1                                          0xF40140UL
#define ADSP_X_ZeroSig10                                         0xF40149UL
#define ADSP_X_ZeroSig11                                         0xF4014AUL
#define ADSP_X_ZeroSig12                                         0xF4014BUL
#define ADSP_X_ZeroSig13                                         0xF4014CUL
#define ADSP_X_ZeroSig14                                         0xF4014DUL
#define ADSP_X_ZeroSig15                                         0xF4014EUL
#define ADSP_X_ZeroSig2                                          0xF40141UL
#define ADSP_X_ZeroSig3                                          0xF40142UL
#define ADSP_X_ZeroSig4                                          0xF40143UL
#define ADSP_X_ZeroSig5                                          0xF40144UL
#define ADSP_X_ZeroSig6                                          0xF40145UL
#define ADSP_X_ZeroSig7                                          0xF40146UL
#define ADSP_X_ZeroSig8                                          0xF40147UL
#define ADSP_X_ZeroSig9                                          0xF40148UL
#define ADSP_X_ZeroSigL                                          0xF4013FUL
#define ADSP_X_ZeroSigR                                          0xF40140UL
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
