CatKoishi/SAF775X-Radio/User/init.h

#ifndef INIT_H
#define INIT_H

void SYS_Init(void);
void GPIO_Init(void);
void Timer_Init(void);
void ADC_Init(void);
void DAC_Init(void);
void SPI_Init(void);
void I2C_Init(void);
void USART_Init(void);

#endif /* INIT_H */
